laneboysrc/rc-light-controller/mk4-tlc5940-lpc812/tools/webserial-programmer/webapp/README.md

This is a stand-alone webapp that implements the user interface and business logic for programming a .HEX file into the NXP LPC812, LPC832 and LPC824 MCU using an off-the-shelf USB-to-Serial adapter.

Note that a driver for the USB-to-Serial adapter must be installed.

## Build (bundling all source files into a single HTML document)

    ./inline-media.py index.html >../../../../gh-pages/webserial-programmer.html
