laneboysrc/rc-light-controller/doc/Light controller typical package contents.jpg

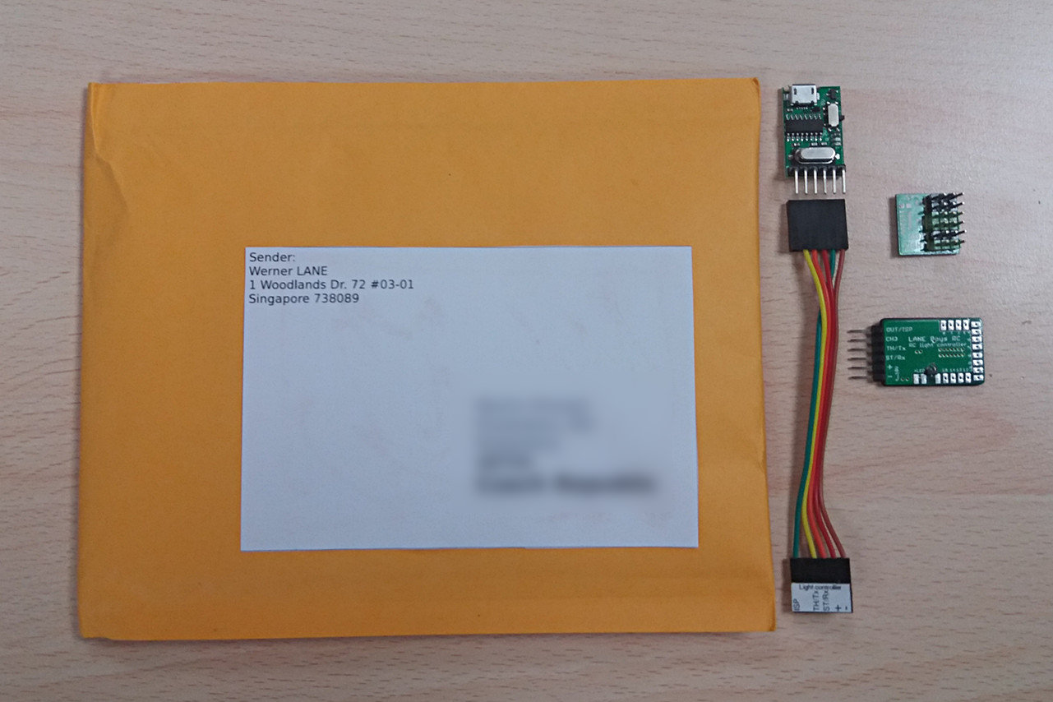
doc/Light controller typical package contents.jpg
