laneboysrc/rc-light-controller/doc/light-controller-mk4-tlc5940-lpc812-rev2.jpg

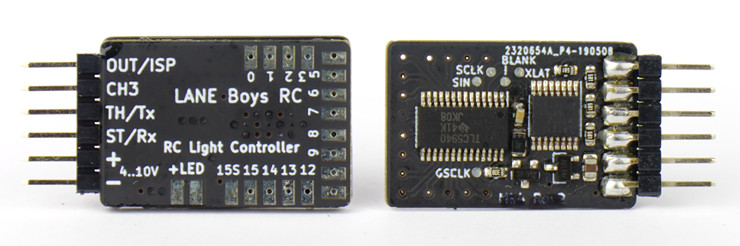
doc/light-controller-mk4-tlc5940-lpc812-rev2.jpg
