laneboysrc/rc-light-controller/doc/mk4-closeup.jpg

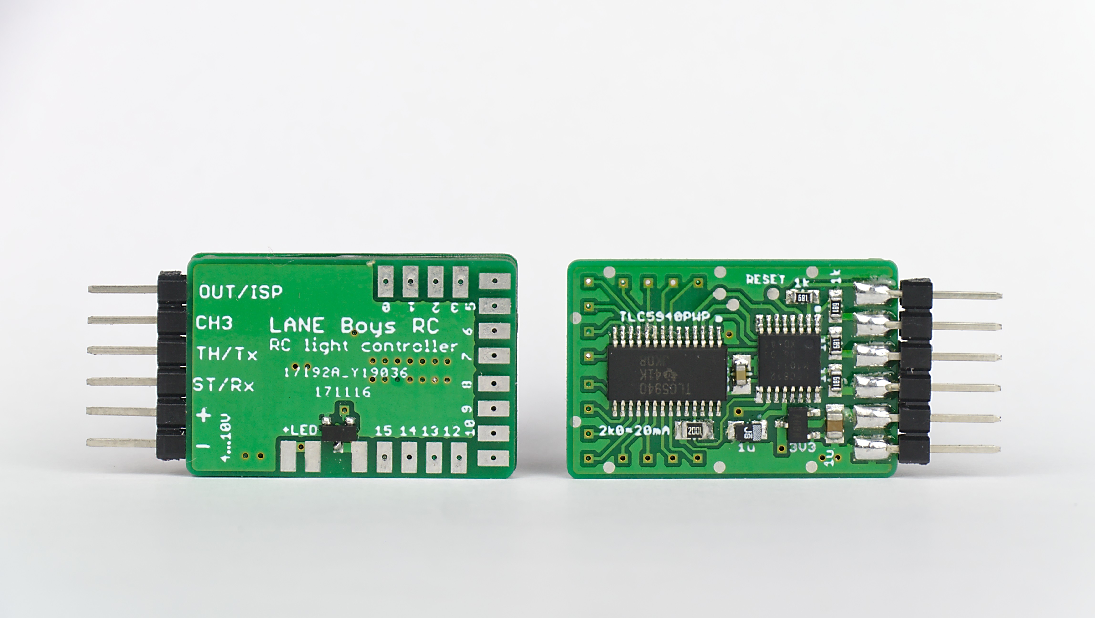
doc/mk4-closeup.jpg
