laneboysrc/rc-light-controller/doc/mk4-rev7-closeup.jpg

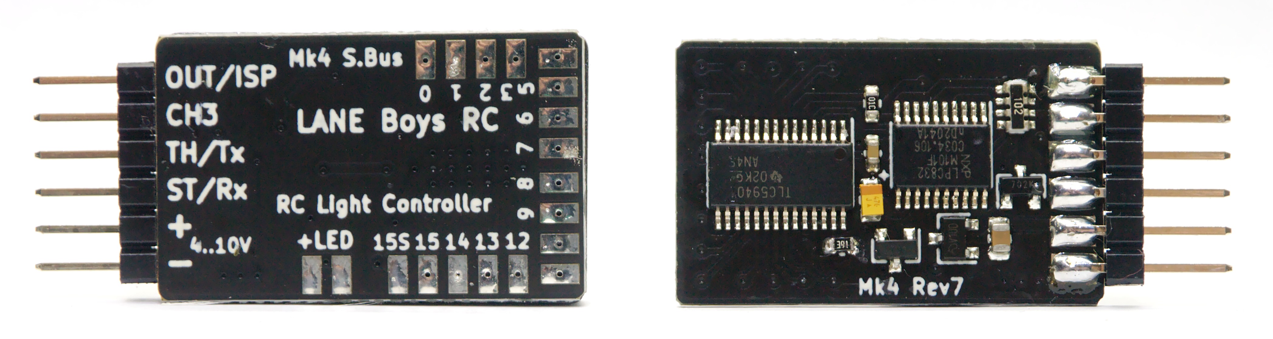
doc/mk4-rev7-closeup.jpg
