laneboysrc/rc-light-controller/doc/mk4-rev7-sbus.jpg

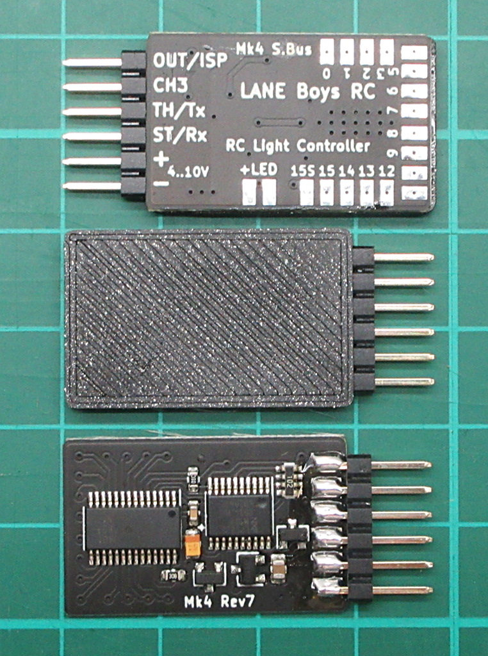
doc/mk4-rev7-sbus.jpg
