laneboysrc/rc-light-controller/doc/mk4-rev7.jpg

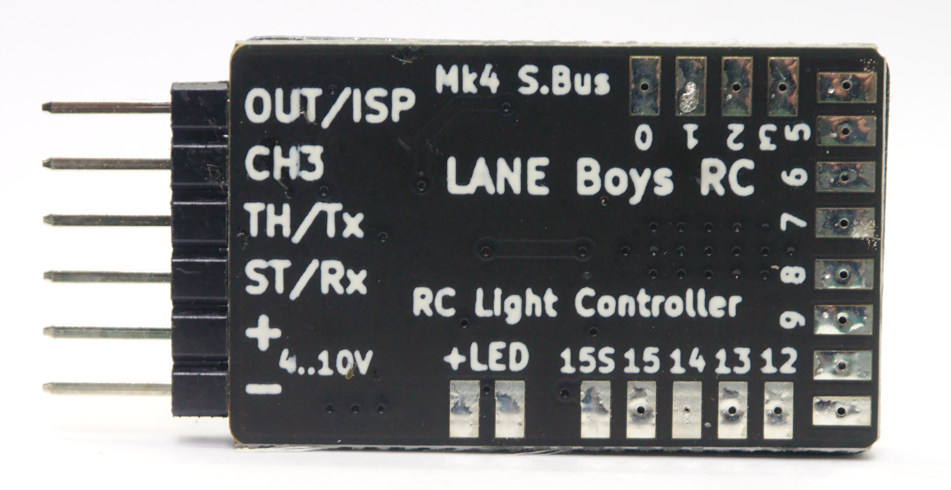
doc/mk4-rev7.jpg
