laneboysrc/rc-light-controller/doc/mk4-single-closeup.jpg

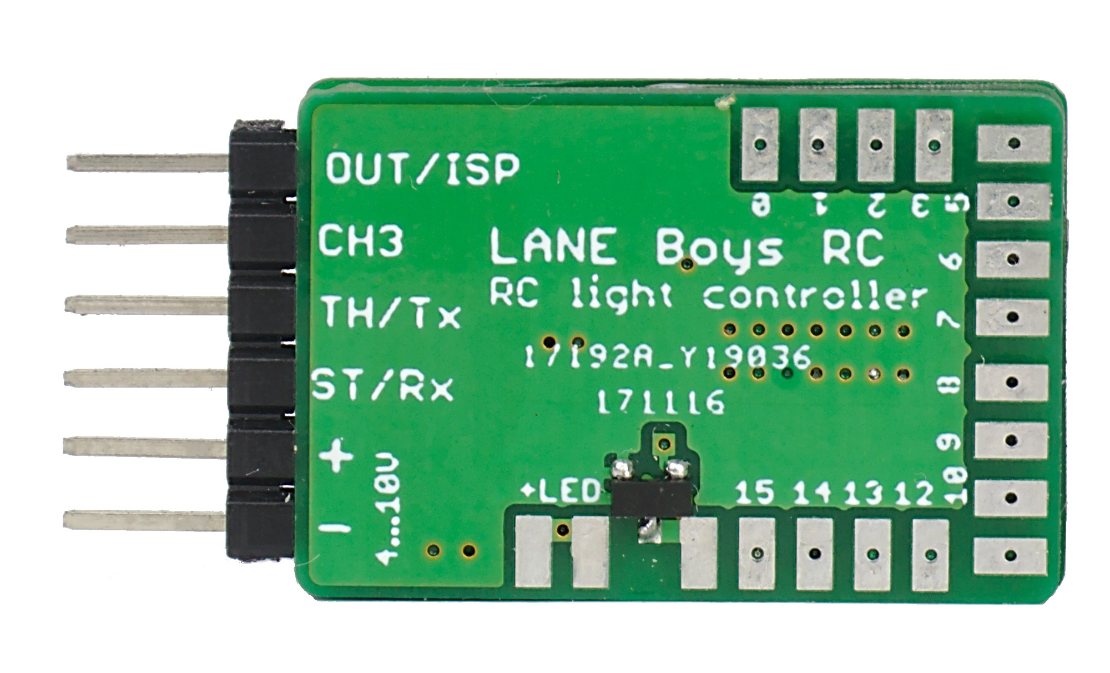
doc/mk4-single-closeup.jpg
