laneboysrc/rc-light-controller/doc/mk4p-connector-side.jpg

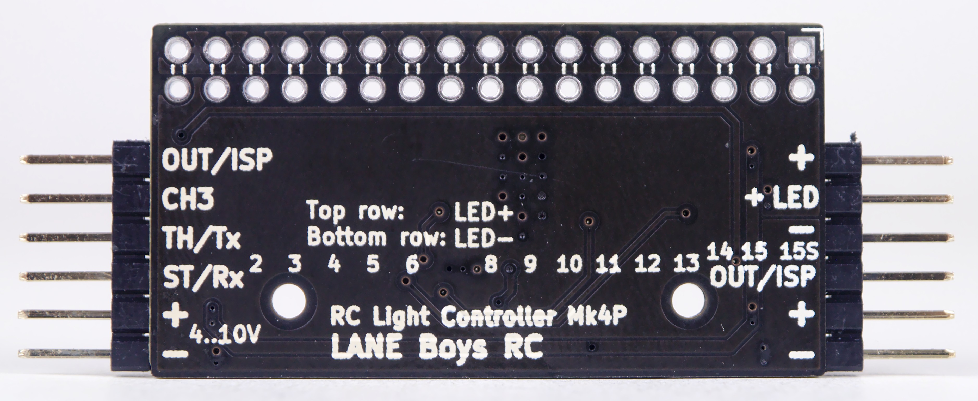
doc/mk4p-connector-side.jpg
