laneboysrc/rc-light-controller/doc/mk4p-front-and-back.jpg

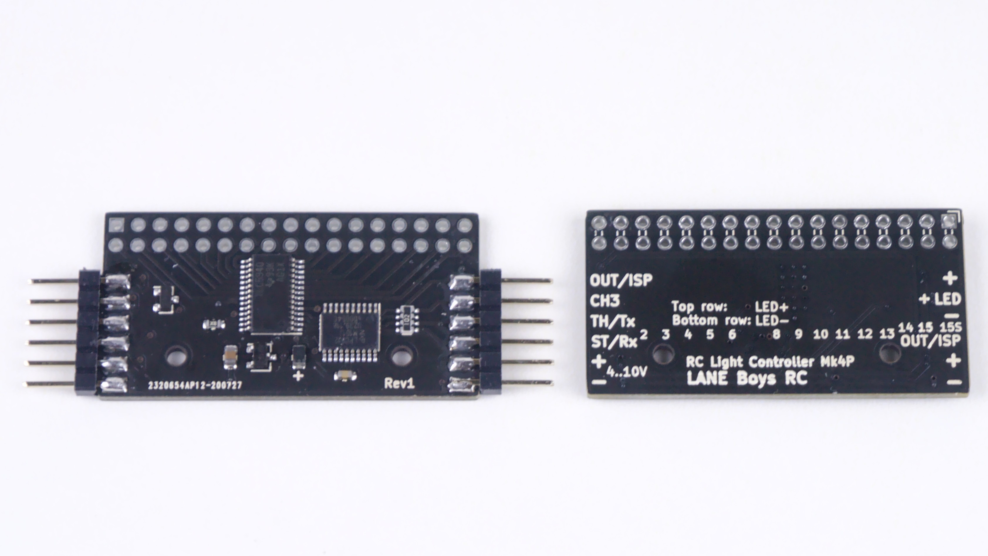
doc/mk4p-front-and-back.jpg
