laneboysrc/rc-light-controller/doc/mk4p-mk4s-led-connector.jpg

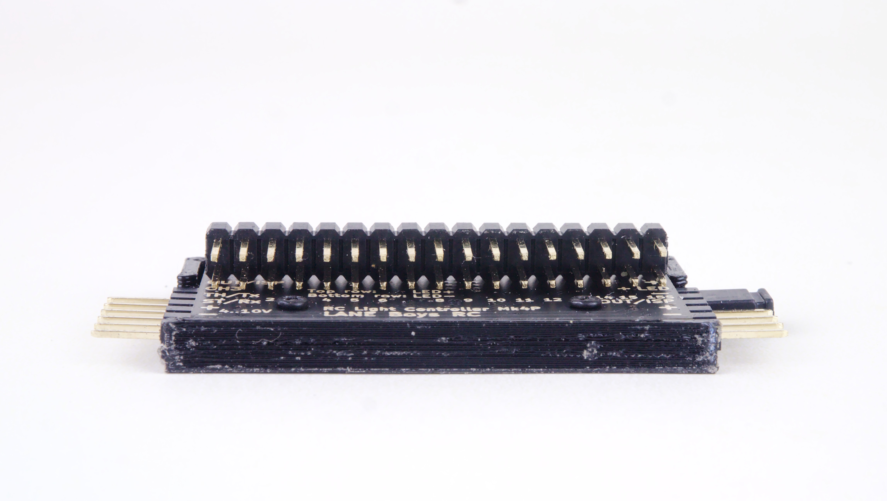
doc/mk4p-mk4s-led-connector.jpg
