laneboysrc/rc-light-controller/doc/mk4p-mk4s-led-supply-options.jpg

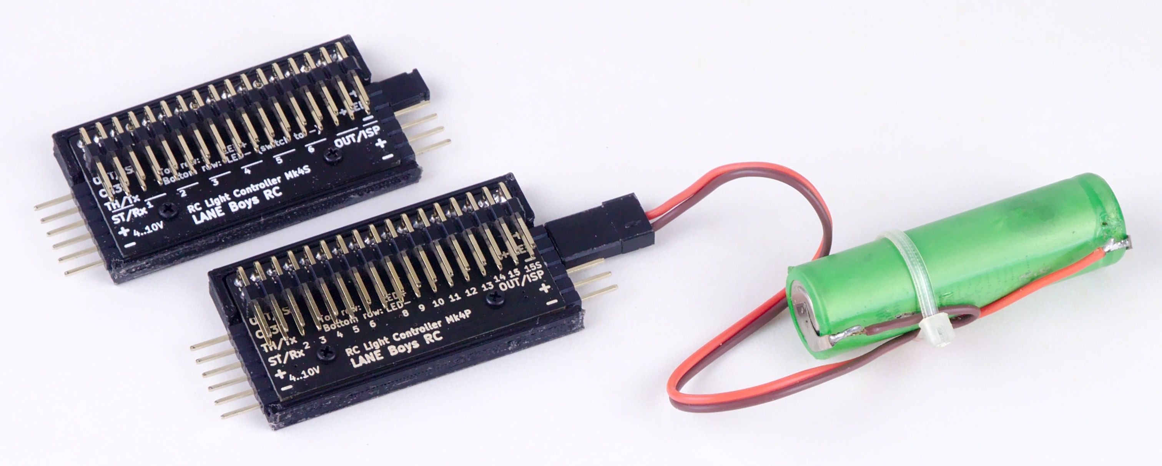
doc/mk4p-mk4s-led-supply-options.jpg
