laneboysrc/rc-light-controller/doc/mk4p-mk4s-together.jpg

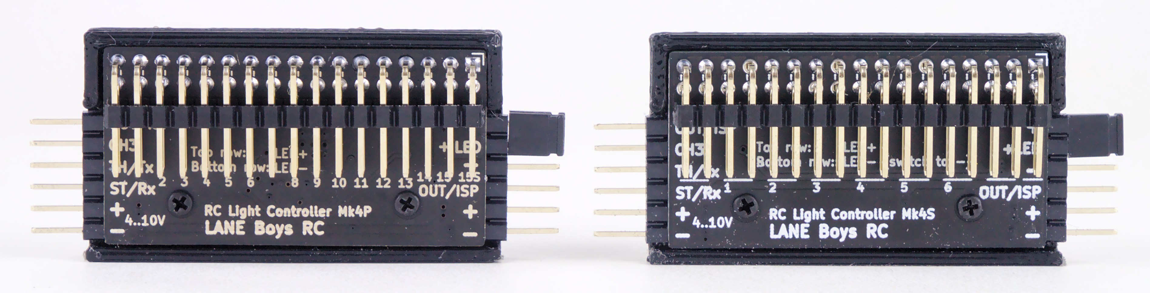
doc/mk4p-mk4s-together.jpg
