laneboysrc/rc-light-controller/doc/mk4s-connector-side.jpg

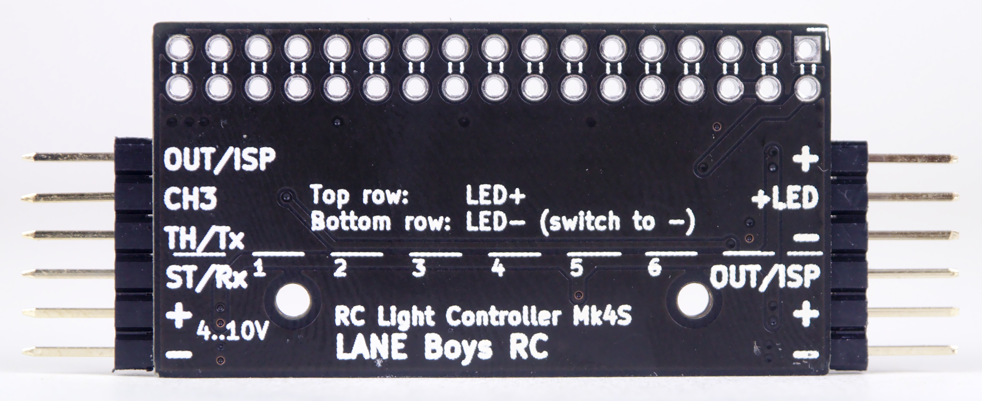
doc/mk4s-connector-side.jpg
