laneboysrc/rc-light-controller/doc/mk4s-front-and-back.jpg

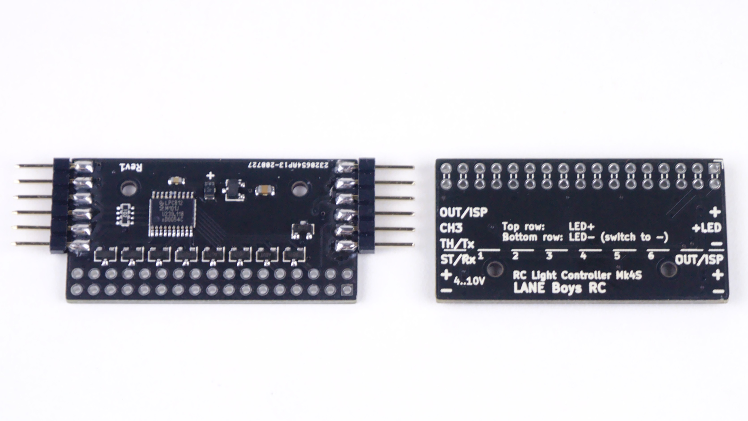
doc/mk4s-front-and-back.jpg
