laneboysrc/rc-light-controller/doc/servo-connected-to-light-controller.png

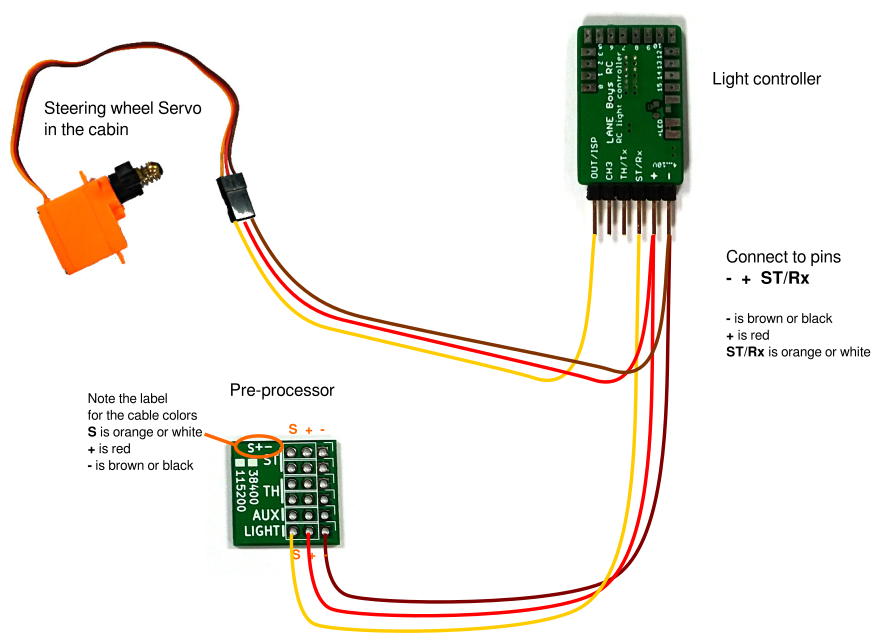
doc/servo-connected-to-light-controller.png
