laneboysrc/rc-light-controller/doc/servo-reader-custom-cable.jpg

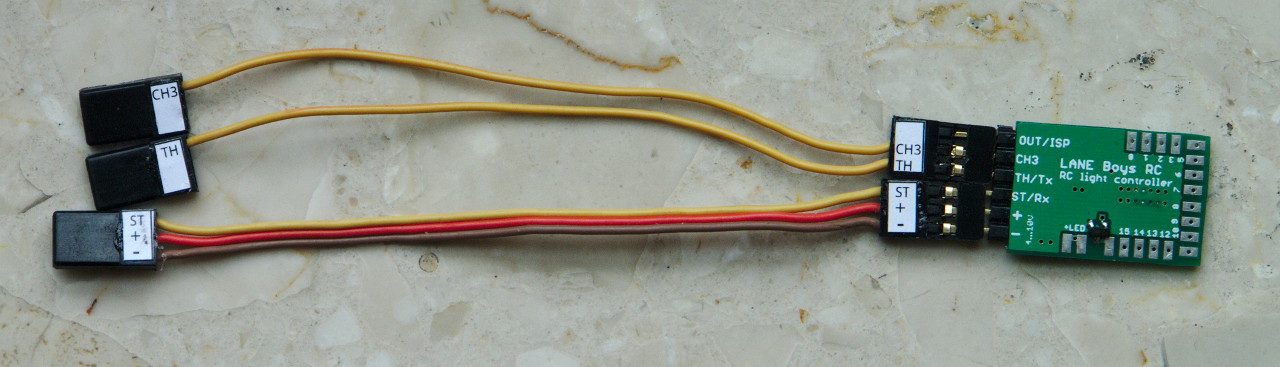
doc/servo-reader-custom-cable.jpg
