laneboysrc/rc-light-controller/doc/src/esc.jpg

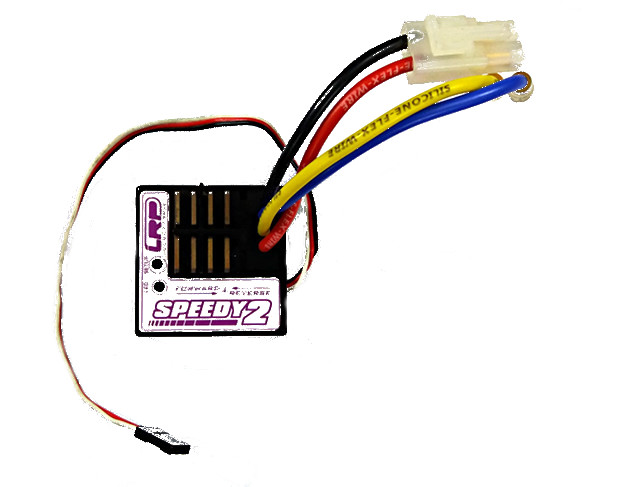
doc/src/esc.jpg
