laneboysrc/rc-light-controller/doc/src/lcp81x_isp..png

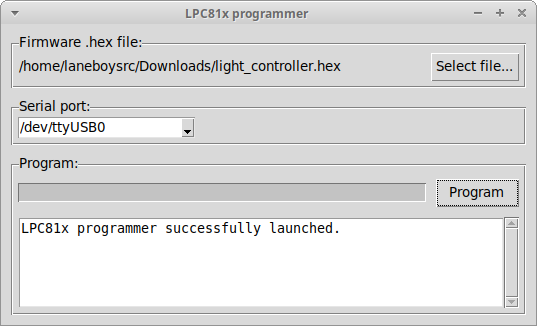
doc/src/lcp81x_isp..png
