laneboysrc/rc-light-controller/doc/src/led_smd_sizes.jpg

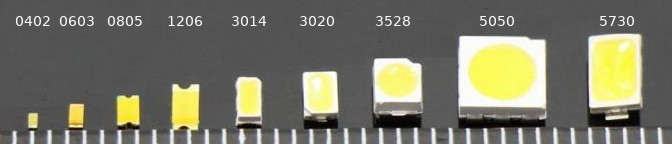
doc/src/led_smd_sizes.jpg
