laneboysrc/rc-light-controller/doc/src/led_throughole.jpg

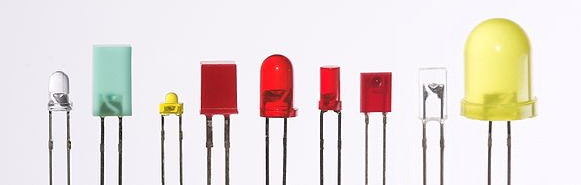
doc/src/led_throughole.jpg
