laneboysrc/rc-light-controller/doc/src/mk4p-rev3-highlighted.jpg

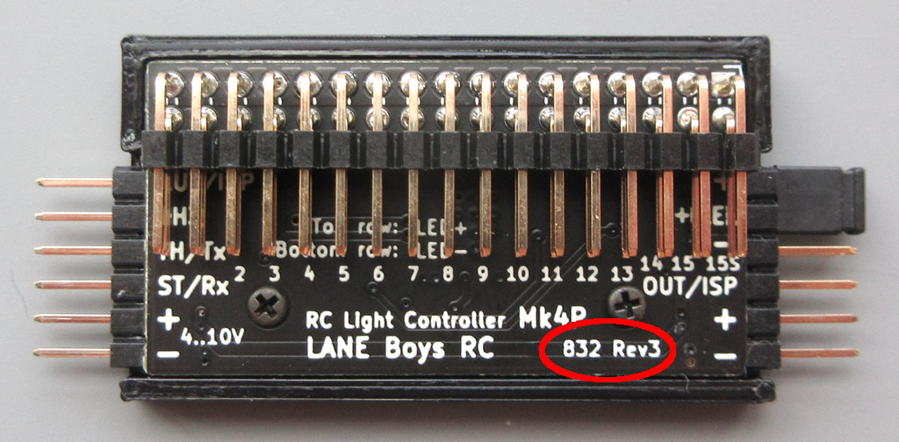
doc/src/mk4p-rev3-highlighted.jpg
