laneboysrc/rc-light-controller/doc/src/preprocessor-5ch.png

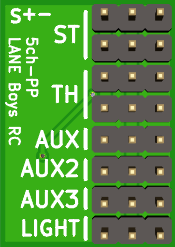
doc/src/preprocessor-5ch.png
