laneboysrc/rc-light-controller/doc/src/pushbutton-round.png

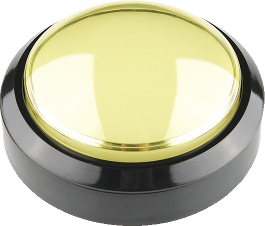
doc/src/pushbutton-round.png
