laneboysrc/rc-light-controller/doc/src/pushbutton.jpg

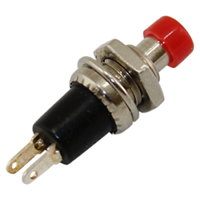
doc/src/pushbutton.jpg
