laneboysrc/rc-light-controller/doc/src/receiver-FGr4S.png

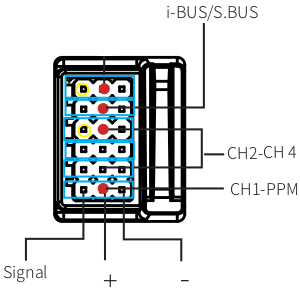
doc/src/receiver-FGr4S.png
