laneboysrc/rc-light-controller/doc/src/servo-pos1.png

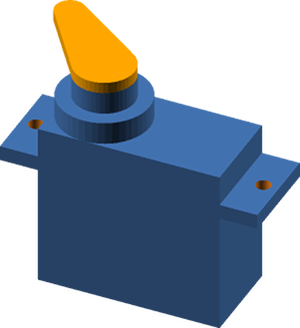
doc/src/servo-pos1.png
