laneboysrc/rc-light-controller/doc/src/servo-pos2.png

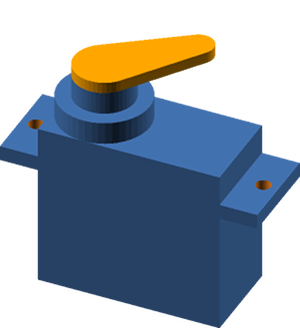
doc/src/servo-pos2.png
