laneboysrc/rc-light-controller/doc/src/servo-reader-diagram-master-slave.png

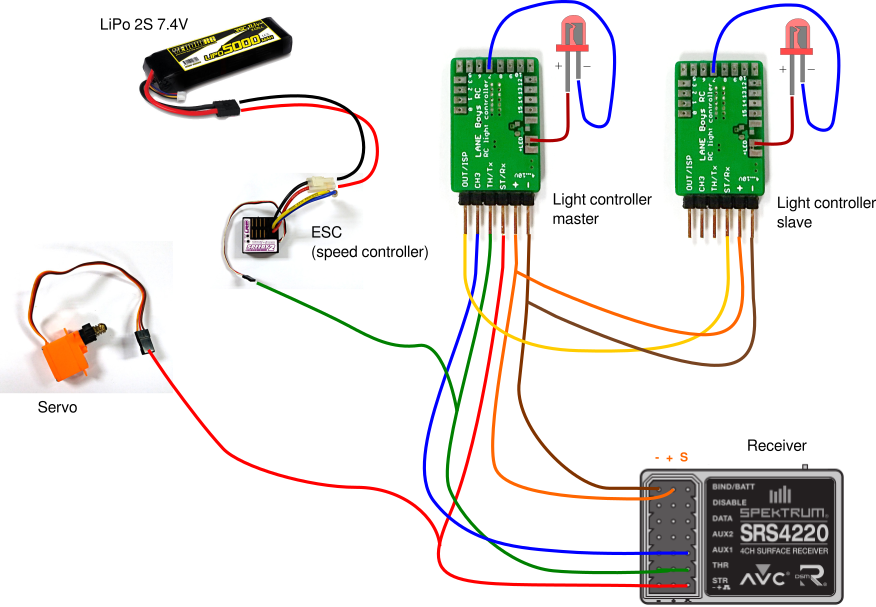
doc/src/servo-reader-diagram-master-slave.png
