laneboysrc/rc-light-controller/doc/src/servo.jpg

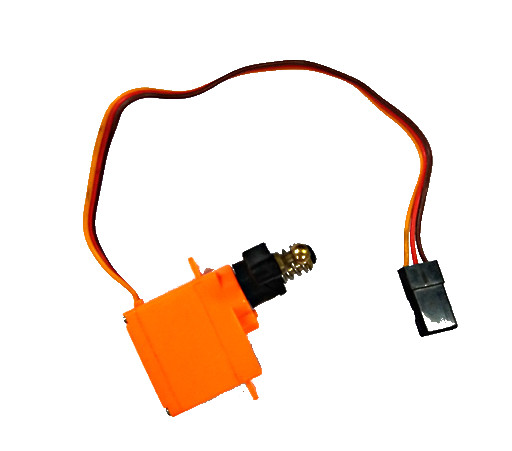
doc/src/servo.jpg
