laneboysrc/rc-light-controller/doc/src/slide-switch.png

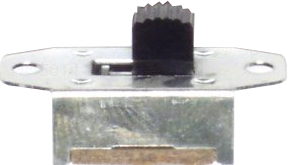
doc/src/slide-switch.png
