laneboysrc/rc-light-controller/doc/src/up-down-button.png

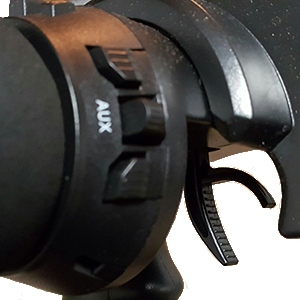
doc/src/up-down-button.png
