laneboysrc/rc-light-controller/doc/src/usb-to-serial-back.jpg

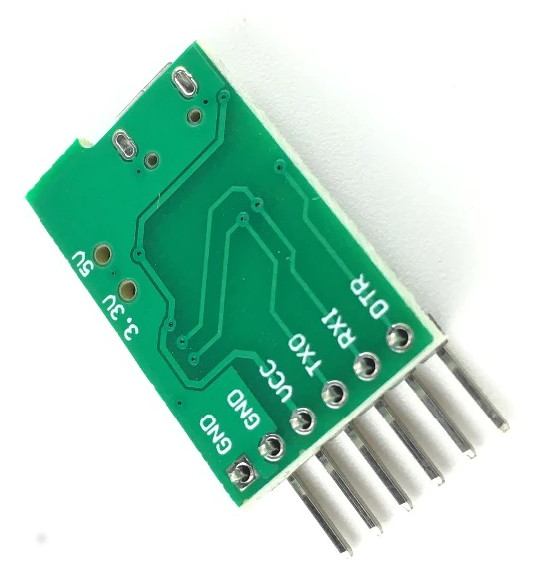
doc/src/usb-to-serial-back.jpg
