laneboysrc/rc-light-controller/doc/src/usb-to-serial-front.jpg

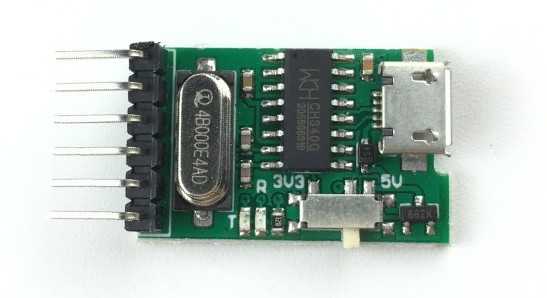
doc/src/usb-to-serial-front.jpg
