laneboysrc/rc-light-controller/doc/src/webusb-programmer-rev3.jpg

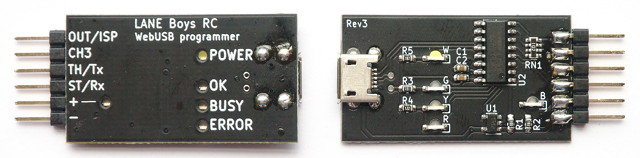
doc/src/webusb-programmer-rev3.jpg
