laneboysrc/rc-light-controller/doc/src/webusb-programming.png

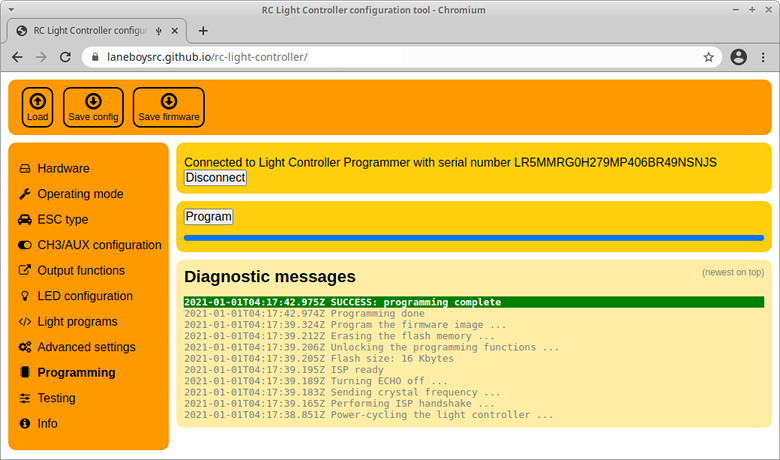
doc/src/webusb-programming.png
