laneboysrc/rc-light-controller/mk4-tlc5940-lpc812/tools/configurator/src/mk4.png

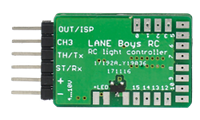
mk4-tlc5940-lpc812/tools/configurator/src/mk4.png
