laneboysrc/rc-light-controller/preprocessor/pre-processor-programming.png

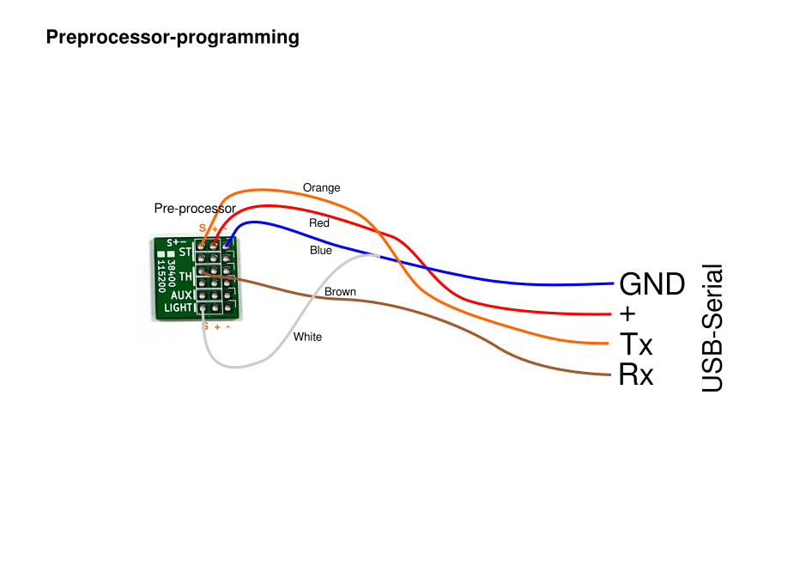
preprocessor/pre-processor-programming.png
