laneboysrc/rc-light-controller/preprocessor/servo-and-esc-wire-splitter/01-distribution-board-top.jpg

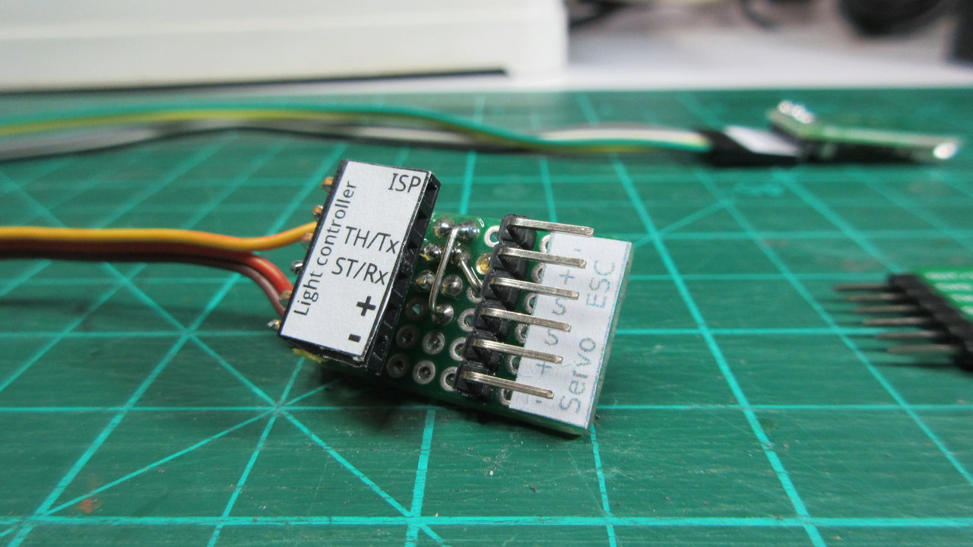
preprocessor/servo-and-esc-wire-splitter/01-distribution-board-top.jpg
