laneboysrc/rc-light-controller/preprocessor/servo-and-esc-wire-splitter/02-distribution-board-bottom.jpg

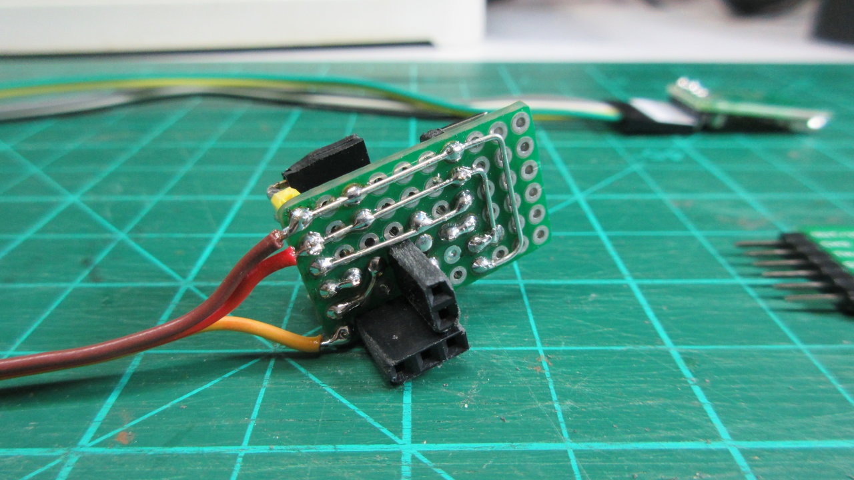
preprocessor/servo-and-esc-wire-splitter/02-distribution-board-bottom.jpg
