laneboysrc/rc-light-controller/preprocessor/servo-and-esc-wire-splitter/03-servo-and-esc-connected.jpg

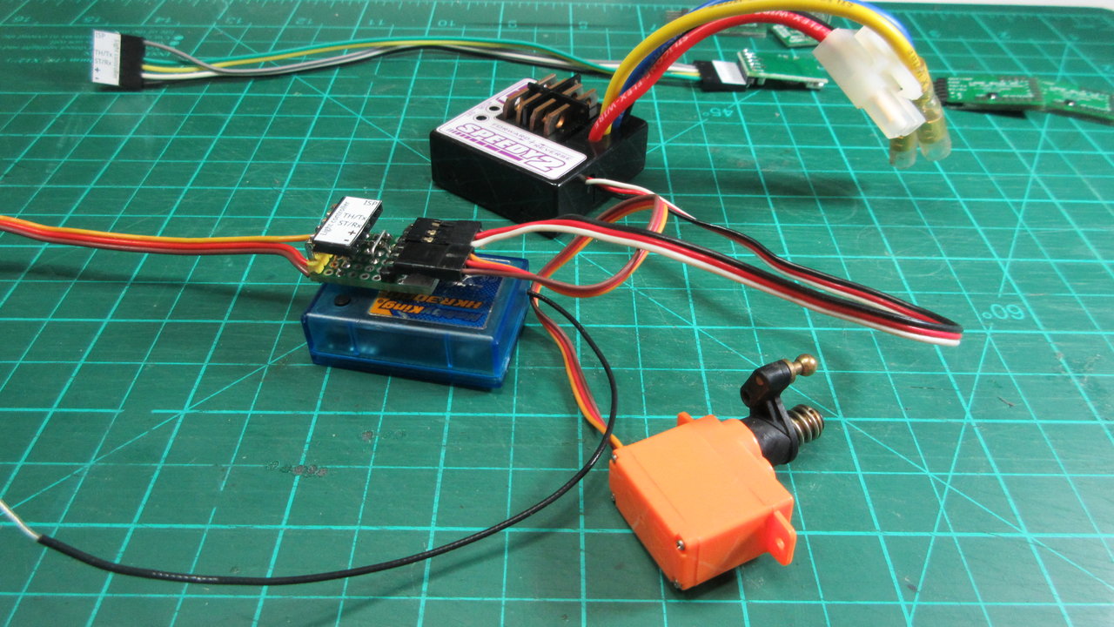
preprocessor/servo-and-esc-wire-splitter/03-servo-and-esc-connected.jpg
