laneboysrc/rc-light-controller/preprocessor/servo-and-esc-wire-splitter/04-servo-and-esc-connected-closeup.jpg

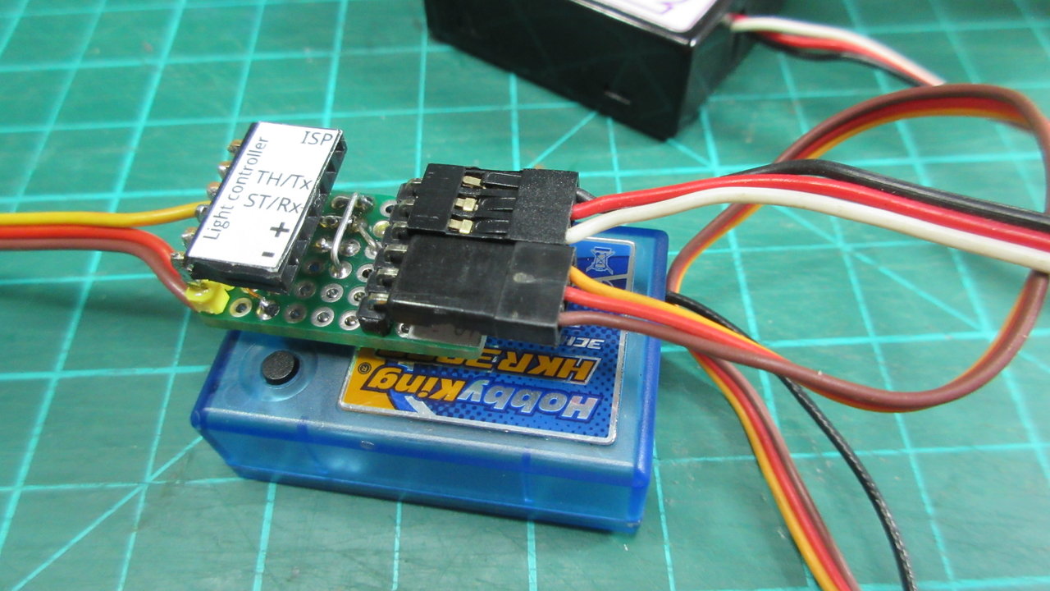
preprocessor/servo-and-esc-wire-splitter/04-servo-and-esc-connected-closeup.jpg
