laneboysrc/rc-light-controller/preprocessor/servo-and-esc-wire-splitter/05-light-controller-connected.jpg

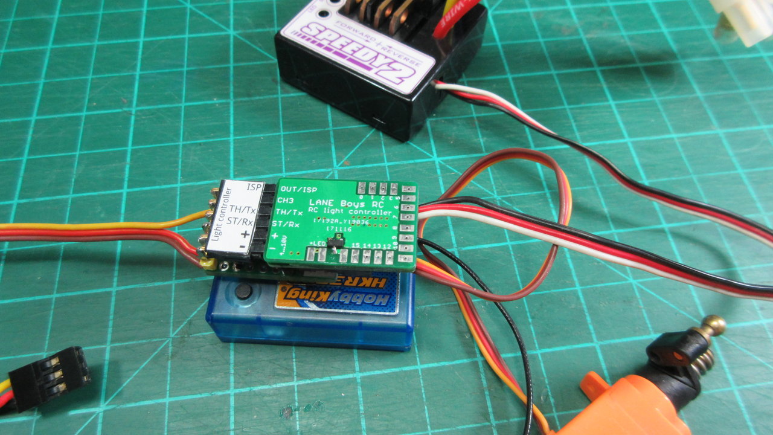
preprocessor/servo-and-esc-wire-splitter/05-light-controller-connected.jpg
