laneboysrc/rc-light-controller/preprocessor/servo-and-esc-wire-splitter/06-all-connections.jpg

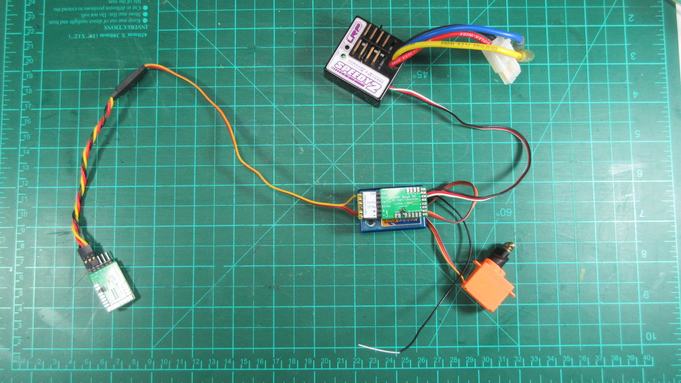
preprocessor/servo-and-esc-wire-splitter/06-all-connections.jpg
