laneboysrc/rc-light-controller/doc/src/webusb-step1.png

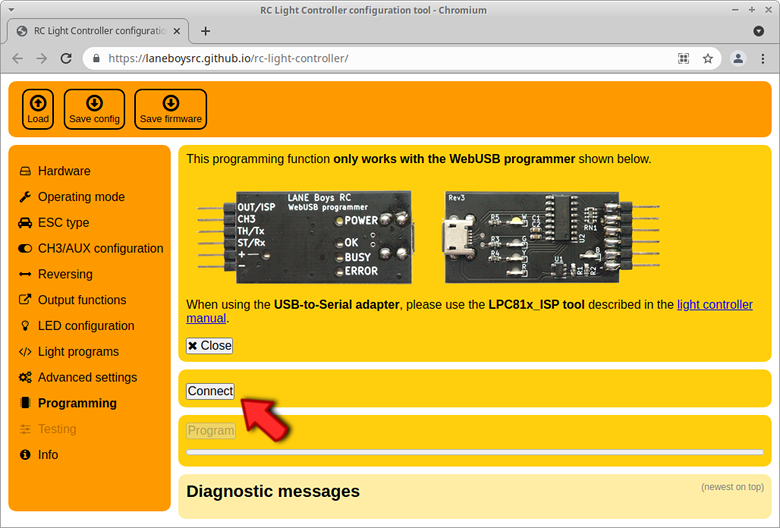
doc/src/webusb-step1.png
