laneboysrc/rc-light-controller/mk4-tlc5940-lpc812/configurations/light_controller.config.land-rover-d110-wiring-diagram.png

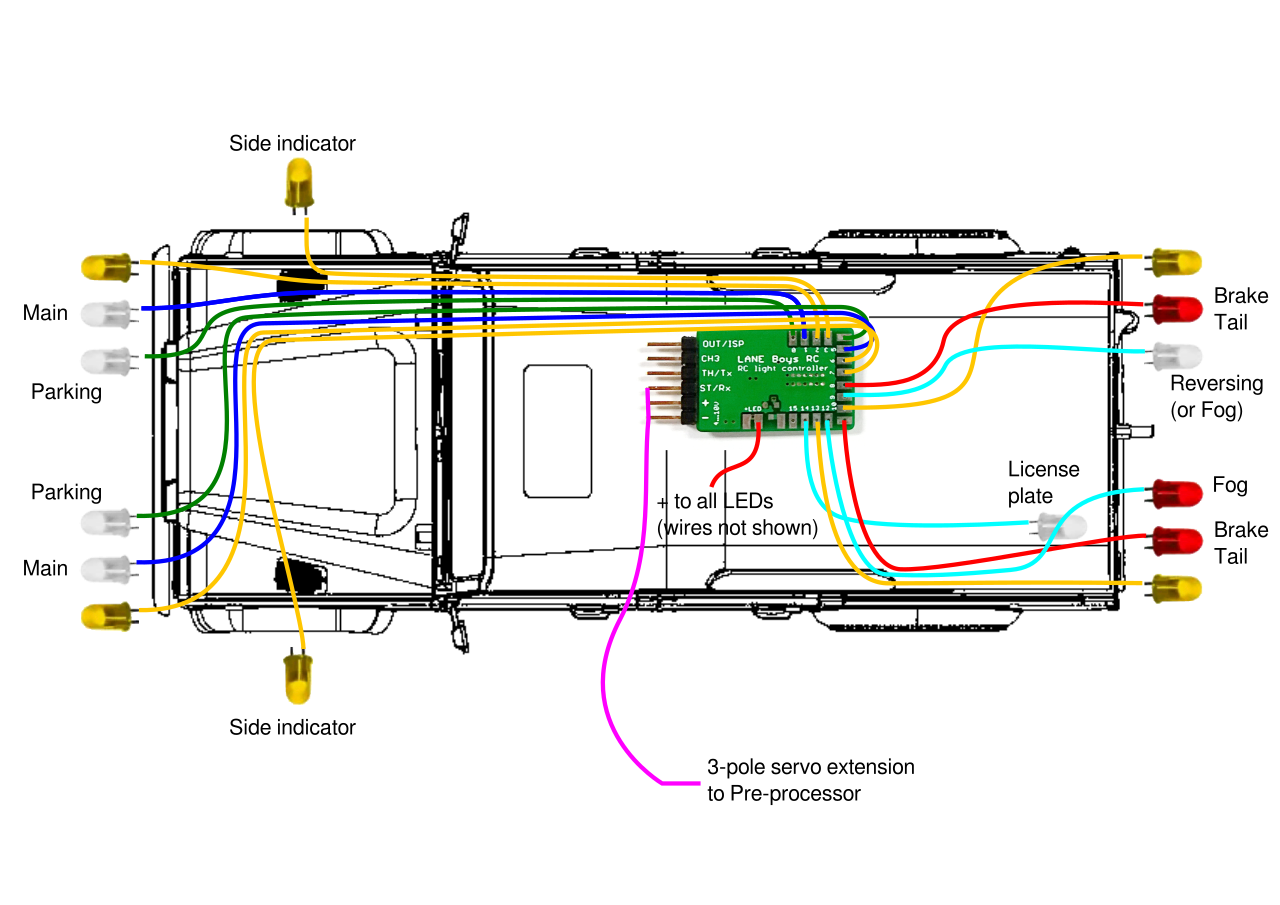
mk4-tlc5940-lpc812/configurations/light_controller.config.land-rover-d110-wiring-diagram.png
