laneboysrc/rc-light-controller/preprocessor/servo-and-esc-wire-splitter/light-controller-distribution-board-wiring.jpg

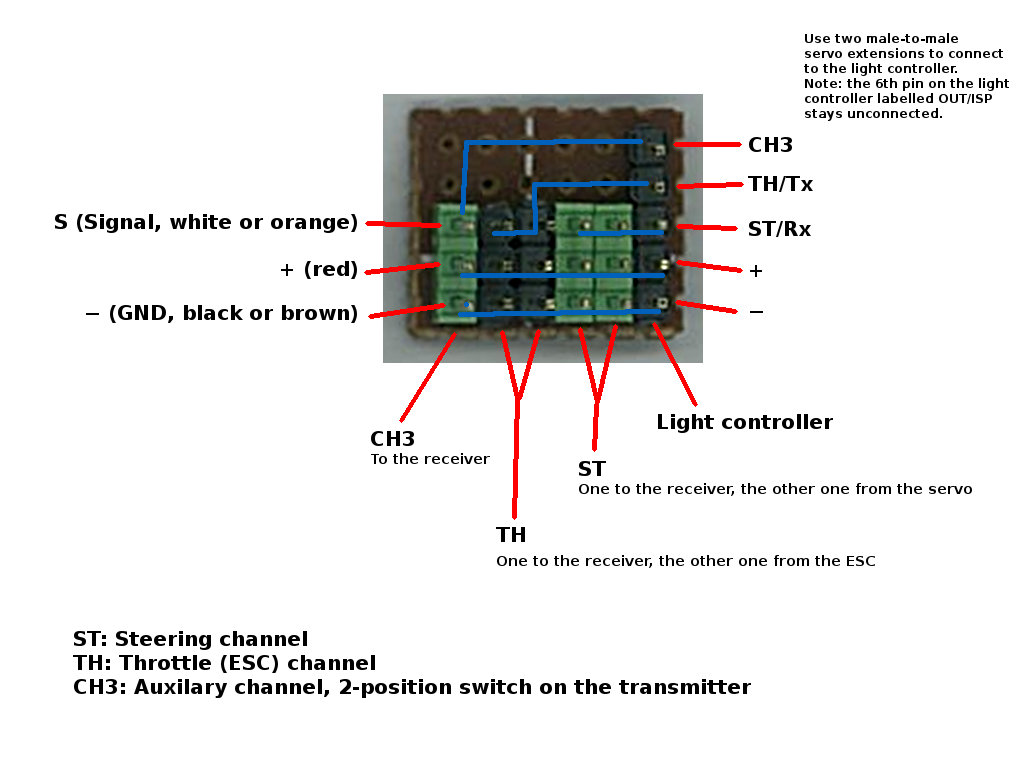
preprocessor/servo-and-esc-wire-splitter/light-controller-distribution-board-wiring.jpg
