laneboysrc/rc-light-controller/doc/src/webusb-testing.png

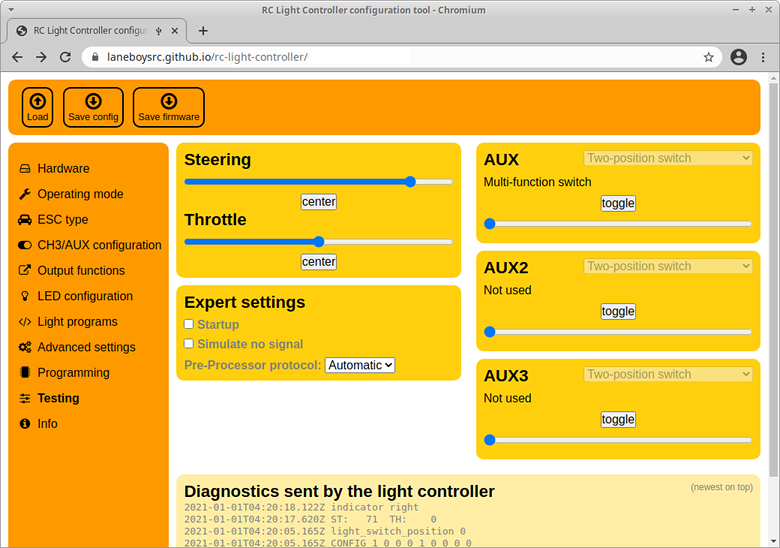
doc/src/webusb-testing.png
