laneboysrc/rc-light-controller/mk4-tlc5940-lpc812/configurations/light_controller.config.school-bus.txt

{
  "config": {
    "firmware_version": 55,
    "mode": 1,
    "esc_mode": 0,
    "slave_output": false,
    "preprocessor_output": false,
    "winch_output": false,
    "steering_wheel_servo_output": true,
    "gearbox_servo_output": false,
    "ws2811_output": false,
    "ch3_is_local_switch": false,
    "ch3_is_momentary": false,
    "auto_brake_lights_forward_enabled": true,
    "auto_brake_lights_reverse_enabled": true,
    "ch3_is_two_button": false,
    "reverse_st": false,
    "reverse_th": false,
    "reverse_aux": false,
    "reverse_aux2": false,
    "reverse_aux3": false,
    "auto_brake_counter_value_forward_min": 25,
    "auto_brake_counter_value_forward_max": 125,
    "auto_brake_counter_value_reverse_min": 25,
    "auto_brake_counter_value_reverse_max": 125,
    "auto_reverse_counter_value_min": 40,
    "auto_reverse_counter_value_max": 100,
    "brake_disarm_counter_value": 50,
    "blink_counter_value": 17,
    "indicator_idle_time_value": 25,
    "indicator_off_timeout_value": 100,
    "centre_threshold_low": 8,
    "centre_threshold_high": 12,
    "blink_threshold": 30,
    "light_switch_positions": 1,
    "initial_light_switch_position": 0,
    "initial_endpoint_delta": 250,
    "ch3_multi_click_timeout": 25,
    "baudrate": 115200,
    "no_signal_timeout": 25,
    "number_of_gears": 2,
    "gearbox_servo_active_time": 50,
    "gearbox_servo_idle_time": 450,
    "servo_pulse_min": 600,
    "servo_pulse_max": 2500,
    "startup_time": 100,
    "multi_aux": true,
    "shelf_queen_mode": true,
    "us_style_combined_lights": true,
    "gearbox_light_program_control": false,
    "light_program_servo_output": false,
    "indicators_while_driving": false,
    "require_extra_click": false,
    "prefer_all_lights_off": false,
    "invert_out15s": false,
    "assign_uart_to_out": false,
    "blink_counter_value_dark": 17,
    "aux_type": 0,
    "aux_function": 1,
    "aux2_type": 3,
    "aux2_function": 0,
    "aux3_type": 0,
    "aux3_function": 0,
    "aux_centre_threshold_low": -10,
    "aux_centre_threshold_high": 10,
    "aux_left_centre_threshold_low": -40,
    "aux_left_centre_threshold_high": -30,
    "aux_centre_right_threshold_low": 30,
    "aux_centre_right_threshold_high": 40,
    "diagnostics_brightness": 255,
    "channel_offset": 3,
    "light_switch_hysteresis": 50,
    "light_switch_centers": [
      0,
      0,
      0,
      0,
      0,
      0,
      0,
      0,
      0
    ]
  },
  "local_leds": {
    "0": {
      "max_change_per_systick": 0,
      "reduction_percent": 0,
      "weak_light_switch_position0": false,
      "weak_light_switch_position1": false,
      "weak_light_switch_position2": false,
      "weak_light_switch_position3": false,
      "weak_light_switch_position4": false,
      "weak_light_switch_position5": false,
      "weak_light_switch_position6": false,
      "weak_light_switch_position7": false,
      "weak_light_switch_position8": false,
      "weak_tail_light": false,
      "weak_brake_light": false,
      "weak_reversing_light": false,
      "weak_indicator_left": false,
      "weak_indicator_right": false,
      "always_on": 0,
      "light_switch_position0": 0,
      "light_switch_position1": 0,
      "light_switch_position2": 0,
      "light_switch_position3": 0,
      "light_switch_position4": 0,
      "light_switch_position5": 0,
      "light_switch_position6": 0,
      "light_switch_position7": 0,
      "light_switch_position8": 0,
      "tail_light": 0,
      "brake_light": 0,
      "reversing_light": 0,
      "indicator_left": 0,
      "indicator_right": 0,
      "diagnostics": 0,
      "name": ""
    },
    "1": {
      "max_change_per_systick": 0,
      "reduction_percent": 0,
      "weak_light_switch_position0": false,
      "weak_light_switch_position1": false,
      "weak_light_switch_position2": false,
      "weak_light_switch_position3": false,
      "weak_light_switch_position4": false,
      "weak_light_switch_position5": false,
      "weak_light_switch_position6": false,
      "weak_light_switch_position7": false,
      "weak_light_switch_position8": false,
      "weak_tail_light": false,
      "weak_brake_light": false,
      "weak_reversing_light": false,
      "weak_indicator_left": false,
      "weak_indicator_right": false,
      "always_on": 0,
      "light_switch_position0": 0,
      "light_switch_position1": 0,
      "light_switch_position2": 0,
      "light_switch_position3": 0,
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
      "indicator_right": 0,
      "diagnostics": 0,
      "name": ""
    },
    "15": {
      "max_change_per_systick": 0,
      "reduction_percent": 0,
      "weak_light_switch_position0": false,
      "weak_light_switch_position1": false,
      "weak_light_switch_position2": false,
      "weak_light_switch_position3": false,
      "weak_light_switch_position4": false,
      "weak_light_switch_position5": false,
      "weak_light_switch_position6": false,
      "weak_light_switch_position7": false,
      "weak_light_switch_position8": false,
      "weak_tail_light": false,
      "weak_brake_light": false,
      "weak_reversing_light": false,
      "weak_indicator_left": false,
      "weak_indicator_right": false,
      "always_on": 0,
      "light_switch_position0": 0,
      "light_switch_position1": 0,
      "light_switch_position2": 0,
      "light_switch_position3": 0,
      "light_switch_position4": 0,
      "light_switch_position5": 0,
      "light_switch_position6": 0,
      "light_switch_position7": 0,
      "light_switch_position8": 0,
      "tail_light": 0,
      "brake_light": 0,
      "reversing_light": 0,
      "indicator_left": 0,
      "indicator_right": 0,
      "diagnostics": 0,
      "name": ""
    },
    "led_count": 16
  },
  "gamma": {
    "gamma_value": "1.8"
  },
  "light_programs": "// Canada school bus yellow and red warning light\n// Based on https://www.youtube.com/watch?v=-NQjBX6ZlSU\n// The school bus has 8 lights: \n// OUT0: yellow front left\n// OUT1: red left front \n// OUT2: red right front \n// OUT3: yellow right front \n// OUT4: yellow left rear\n// OUT5: red left rear\n// OUT6: red right rear\n// OUT7: yellow right rear\n//\n// A 3-position switch on the transmitter is connected to AUX2.\n// The switch sequence is off -> yellow -> red\n//\n// The AUX2 channel is monitored in a \"run always\" light program\n// and setting the special variables program-state-0 and program-state1.\n// A light program for the YELLOW LEDs is run when program-state-0 is set to \"1\".\n// A light program for the RED LEDs is run when program-state-1 is set to \"1\".\n\nrun always\n\nloop:\n\tsleep 20\n    if aux2 < -33\n    goto off\n    if aux2 < 33\n    goto yellow\n    // if aux2 >= 33 then do red\nred:    \n\t// Switch off yellow, turn on red\n\tprogram-state-0 = 0\n\tprogram-state-1 = 1\t\n    goto loop\n\nyellow:    \n\t// Switch on yellow, turn of red\n\tprogram-state-0 = 1\n\tprogram-state-1 = 0\n    goto loop\n\noff:    \n\t// Switch of yellow and red\n\tprogram-state-0 = 0\n\tprogram-state-1 = 0\n    goto loop\n\nend\n\n// Light program for flashing of yellow lights\nrun when program-state-0\n\nled ylf = led[1] \t// yellow left front\nled yrf = led[2] \t// yellow right front\nled ylr = led[5] \t// yellow left rear\nled yrr = led[6] \t// yellow right rear\n\n// According to the video the lights never go fully dark, \n// so we toggle between a minimum and maximum brightness\nconst BRIGHTNESS_MIN = 15\nconst BRIGHTNESS_MAX = 100\n// FADE_TIMING determines how quickly the LEDs fade. \n// Expimentation is required to determine which value \n// gives a good experience.\nconst FADE_TIMING = 3\n// According to the video the blink sequence is \n// 0.5 seconds off, 0.5 seconds on.\nconst TIME_PERIOD = 500\n\nloop:\n\tfade all leds stepsize FADE_TIMING\n    ylf, ylr = BRIGHTNESS_MAX\n    yrf, yrr = BRIGHTNESS_MIN\n    sleep TIME_PERIOD\n    ylf, ylr = BRIGHTNESS_MIN\n    yrf, yrr = BRIGHTNESS_MAX\n    sleep TIME_PERIOD\n\tgoto loop\n\nend\n\n// Light program for flashing of red lights\nrun when program-state-1\n\nled rlf = led[0] \t// red left front\nled rrf = led[3] \t// red right front\nled rlr = led[4] \t// red left rear\nled rrr = led[7] \t// red right rear\n\nconst BRIGHTNESS_MIN = 15\nconst BRIGHTNESS_MAX = 100\nconst FADE_TIMING = 3\nconst TIME_PERIOD = 500\n\nloop:\n\tfade all leds stepsize FADE_TIMING\n    rlf, rlr = BRIGHTNESS_MAX\n    rrf, rrr = BRIGHTNESS_MIN\n    sleep TIME_PERIOD\n    rlf, rlr = BRIGHTNESS_MIN    \n    rrf, rrr = BRIGHTNESS_MAX\n    sleep TIME_PERIOD\n\tgoto loop\n\nend"
}
