laneboysrc/rc-light-controller/mk4-tlc5940-lpc812/configurations/light_controller.config.up-down-sequential-light-switch.txt

{
  "config": {
    "firmware_version": 44,
    "mode": 1,
    "esc_mode": 0,
    "slave_output": false,
    "preprocessor_output": false,
    "steering_wheel_servo_output": true,
    "gearbox_servo_output": false,
    "ch3_is_local_switch": false,
    "ch3_is_momentary": false,
    "auto_brake_lights_forward_enabled": true,
    "auto_brake_lights_reverse_enabled": true,
    "ch3_is_two_button": false,
    "reverse_st": false,
    "reverse_th": false,
    "reverse_aux": false,
    "reverse_aux2": false,
    "reverse_aux3": false,
    "auto_brake_counter_value_forward_min": 25,
    "auto_brake_counter_value_forward_max": 125,
    "auto_brake_counter_value_reverse_min": 25,
    "auto_brake_counter_value_reverse_max": 125,
    "auto_reverse_counter_value_min": 40,
    "auto_reverse_counter_value_max": 100,
    "brake_disarm_counter_value": 50,
    "blink_counter_value": 17,
    "indicator_idle_time_value": 25,
    "indicator_off_timeout_value": 100,
    "centre_threshold_low": 8,
    "centre_threshold_high": 12,
    "blink_threshold": 30,
    "light_switch_positions": 5,
    "initial_light_switch_position": 0,
    "initial_endpoint_delta": 250,
    "ch3_multi_click_timeout": 25,
    "baudrate": 115200,
    "no_signal_timeout": 25,
    "number_of_gears": 2,
    "gearbox_servo_active_time": 50,
    "gearbox_servo_idle_time": 450,
    "servo_pulse_min": 600,
    "servo_pulse_max": 2500,
    "startup_time": 100,
    "multi_aux": true,
    "shelf_queen_mode": true,
    "us_style_combined_lights": true,
    "gearbox_light_program_control": false,
    "light_program_servo_output": false,
    "indicators_while_driving": false,
    "require_extra_click": false,
    "prefer_all_lights_off": false,
    "invert_out15s": false,
    "assign_uart_to_out": false,
    "blink_counter_value_dark": 17,
    "aux_type": 0,
    "aux_function": 1,
    "aux2_type": 3,
    "aux2_function": 0,
    "aux3_type": 0,
    "aux3_function": 0,
    "aux_centre_threshold_low": -10,
    "aux_centre_threshold_high": 10,
    "aux_left_centre_threshold_low": -40,
    "aux_left_centre_threshold_high": -30,
    "aux_centre_right_threshold_low": 30,
    "aux_centre_right_threshold_high": 40,
    "diagnostics_brightness": 255,
    "light_switch_hysteresis": 10,
    "light_switch_centers": [
      -80,
      -40,
      0,
      40,
      80,
      0,
      0,
      0,
      0
    ]
  },
  "local_leds": {
    "0": {
      "max_change_per_systick": 0,
      "reduction_percent": 0,
      "weak_light_switch_position0": false,
      "weak_light_switch_position1": false,
      "weak_light_switch_position2": false,
      "weak_light_switch_position3": false,
      "weak_light_switch_position4": false,
      "weak_light_switch_position5": false,
      "weak_light_switch_position6": false,
      "weak_light_switch_position7": false,
      "weak_light_switch_position8": false,
      "weak_tail_light": false,
      "weak_brake_light": false,
      "weak_reversing_light": false,
      "weak_indicator_left": false,
      "weak_indicator_right": false,
      "always_on": 0,
      "light_switch_position0": 0,
      "light_switch_position1": 255,
      "light_switch_position2": 255,
      "light_switch_position3": 255,
      "light_switch_position4": 255,
      "light_switch_position5": 0,
      "light_switch_position6": 0,
      "light_switch_position7": 0,
      "light_switch_position8": 0,
      "tail_light": 0,
      "brake_light": 0,
      "reversing_light": 0,
      "indicator_left": 0,
      "indicator_right": 0,
      "diagnostics": 0
    },
    "1": {
      "max_change_per_systick": 0,
      "reduction_percent": 0,
      "weak_light_switch_position0": false,
      "weak_light_switch_position1": false,
      "weak_light_switch_position2": false,
      "weak_light_switch_position3": false,
      "weak_light_switch_position4": false,
      "weak_light_switch_position5": false,
      "weak_light_switch_position6": false,
      "weak_light_switch_position7": false,
      "weak_light_switch_position8": false,
      "weak_tail_light": false,
      "weak_brake_light": false,
      "weak_reversing_light": false,
      "weak_indicator_left": false,
      "weak_indicator_right": false,
      "always_on": 0,
      "light_switch_position0": 0,
      "light_switch_position1": 255,
      "light_switch_position2": 255,
      "light_switch_position3": 255,
      "light_switch_position4": 255,
      "light_switch_position5": 0,
      "light_switch_position6": 0,
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
      "weak_tail_light": false,
      "weak_brake_light": false,
      "weak_reversing_light": false,
      "weak_indicator_left": false,
      "weak_indicator_right": false,
      "always_on": 0,
      "light_switch_position0": 0,
      "light_switch_position1": 0,
      "light_switch_position2": 0,
      "light_switch_position3": 0,
      "light_switch_position4": 255,
      "light_switch_position5": 0,
      "light_switch_position6": 0,
      "light_switch_position7": 0,
      "light_switch_position8": 0,
      "tail_light": 0,
      "brake_light": 0,
      "reversing_light": 0,
      "indicator_left": 0,
      "indicator_right": 0,
      "diagnostics": 0
    },
    "led_count": 16
  },
  "gamma": {
    "gamma_value": "1.8"
  },
  "light_programs": "// This light program implements a sequential light switch\n// using an up/down button on a transmitter.\n//\n// This light program requires a 5-channel Pre-Processor.\n// It uses AUX2, but any of the AUX channels can be used.\n//\n// The buttons on the transmitter must have a momentary\n// function: \n// - When no button is pressed, the servo is in the center\n// - While the up button is held, the servo is in position +100\n// - While the down button is held, the servo is in position -100\n\nrun always\n\n// Threshold for the AUX channel to implement a hysteresis\nconst THRESHOLD_LEFT = -66\nconst THRESHOLD_CENTER_LEFT = -33\nconst THRESHOLD_CENTER_RIGHT = 33\nconst THRESHOLD_RIGHT = 66\n\n// Internal state variable to track the AUX signal\nvar state\nconst STATE_WAIT_FOR_CENTER = 0\nconst STATE_CENTER = 1\n\n\nloop:\n\t// We check the AUX channel every 40ms, the\n    // rest of the time the light controller \n    // can do other things\n\tsleep 40\n    \n    // Branch to the action reflecting the current\n    // state\n    if state == STATE_WAIT_FOR_CENTER\n    goto wait_for_center\n    if state == STATE_CENTER\n    goto center\n\n\t// We should never reach here; just in case ...\n    state = STATE_WAIT_FOR_CENTER\n\tgoto loop\n\n\t// Wait for the button to be released (= center).\n    // For the AUX to be in center, the servo signal\n    // must be between THRESHOLD_CENTER_LEFT and\n    // THRESHOLD_CENTER_RIGHT (-33 .. +33)\nwait_for_center:\n\t// If AUX is less than LEFT, the switch is\n    // not in the center\n\tif aux2 < THRESHOLD_CENTER_LEFT\n    goto loop\n\t// If AUX is more than RIGHT, the switch is\n    // not in the center\n\tif aux2 > THRESHOLD_CENTER_RIGHT\n    goto loop\n    // Between LEFT and RIGHT: switch is in the center!\n    state = STATE_CENTER\n\tgoto loop\n    \n    // Switch was centered: detect whether the up\n    // or down button has been pressed\ncenter:\n\t// LEFT threshold exceeded: we have a down button press!\n\tif aux2 < THRESHOLD_LEFT\n    goto down\n\t// RIGHT threshold exceeded: we have an up button press!\n\tif aux2 > THRESHOLD_RIGHT\n    goto up\n\tgoto loop\n\n\t// Down button: decrement the light switch position.\n    // If the light switch position is 0, then we set it\n    // to -1 -- but the light controller checks for that\n    // and \"fixes\" the value back to 0.\ndown:\n\tlight-switch-position -= 1\n    state = STATE_WAIT_FOR_CENTER\n\tgoto loop\n\n\t// Up button: increment the light switch position.\n    // If the light switch ends up beyond the position \n    // defined in the \"LED configuration\" table, the \n    // light controller will \"fix\" it back to the hightest.\n    // used light switch position.\nup:\n\tlight-switch-position += 1\n    state = STATE_WAIT_FOR_CENTER\n\tgoto loop\n\nend"
}
