laneboysrc/rc-light-controller/mk4-tlc5940-lpc812/configurations/light_controller.config.lexus-rcf.txt

{
  "config": {
    "firmware_version": 1,
    "mode": 0,
    "esc_mode": 1,
    "slave_output": false,
    "preprocessor_output": false,
    "winch_output": false,
    "steering_wheel_servo_output": false,
    "gearbox_servo_output": false,
    "ch3_is_local_switch": false,
    "ch3_is_momentary": false,
    "auto_brake_lights_forward_enabled": true,
    "auto_brake_lights_reverse_enabled": true,
    "auto_brake_counter_value_forward_min": 25,
    "auto_brake_counter_value_forward_max": 125,
    "auto_brake_counter_value_reverse_min": 25,
    "auto_brake_counter_value_reverse_max": 125,
    "auto_reverse_counter_value_min": 40,
    "auto_reverse_counter_value_max": 100,
    "brake_disarm_counter_value": 50,
    "blink_counter_value": 17,
    "indicator_idle_time_value": 25,
    "indicator_off_timeout_value": 100,
    "centre_threshold_low": 8,
    "centre_threshold_high": 12,
    "blink_threshold": 30,
    "light_switch_positions": 2,
    "initial_light_switch_position": 0,
    "initial_endpoint_delta": 200,
    "ch3_multi_click_timeout": 15,
    "winch_command_repeat_time": 50,
    "baudrate": 38400,
    "no_signal_timeout": 25,
    "number_of_gears": 2,
    "gearbox_servo_active_time": 50,
    "gearbox_servo_idle_time": 450,
    "servo_pulse_min": 600,
    "servo_pulse_max": 2500,
    "startup_time": 100
  },
  "local_leds": {
    "0": {
      "max_change_per_systick": 0,
      "reduction_percent": 0,
      "weak_light_switch_position0": false,
      "weak_light_switch_position1": false,
      "weak_light_switch_position2": false,
      "weak_light_switch_position3": false,
      "weak_light_switch_position4": false,
      "weak_light_switch_position5": false,
      "weak_light_switch_position6": false,
      "weak_light_switch_position7": false,
      "weak_light_switch_position8": false,
      "weak_tail_light": false,
      "weak_brake_light": false,
      "weak_reversing_light": false,
      "weak_indicator_left": false,
      "weak_indicator_right": false,
      "always_on": 0,
      "light_switch_position0": 0,
      "light_switch_position1": 0,
      "light_switch_position2": 0,
      "light_switch_position3": 0,
      "light_switch_position4": 0,
      "light_switch_position5": 0,
      "light_switch_position6": 0,
      "light_switch_position7": 0,
      "light_switch_position8": 0,
      "tail_light": 0,
      "brake_light": 0,
      "reversing_light": 0,
      "indicator_left": 0,
      "indicator_right": 0
    },
    "1": {
      "max_change_per_systick": 0,
      "reduction_percent": 0,
      "weak_light_switch_position0": false,
      "weak_light_switch_position1": false,
      "weak_light_switch_position2": false,
      "weak_light_switch_position3": false,
      "weak_light_switch_position4": false,
      "weak_light_switch_position5": false,
      "weak_light_switch_position6": false,
      "weak_light_switch_position7": false,
      "weak_light_switch_position8": false,
      "weak_tail_light": false,
      "weak_brake_light": false,
      "weak_reversing_light": false,
      "weak_indicator_left": false,
      "weak_indicator_right": false,
      "always_on": 0,
      "light_switch_position0": 0,
      "light_switch_position1": 0,
      "light_switch_position2": 0,
      "light_switch_position3": 0,
      "light_switch_position4": 0,
      "light_switch_position5": 0,
      "light_switch_position6": 0,
      "light_switch_position7": 0,
      "light_switch_position8": 0,
      "tail_light": 0,
      "brake_light": 0,
      "reversing_light": 0,
      "indicator_left": 0,
      "indicator_right": 0
    },
    "2": {
      "max_change_per_systick": 0,
      "reduction_percent": 0,
      "weak_light_switch_position0": false,
      "weak_light_switch_position1": false,
      "weak_light_switch_position2": false,
      "weak_light_switch_position3": false,
      "weak_light_switch_position4": false,
      "weak_light_switch_position5": false,
      "weak_light_switch_position6": false,
      "weak_light_switch_position7": false,
      "weak_light_switch_position8": false,
      "weak_tail_light": false,
      "weak_brake_light": false,
      "weak_reversing_light": false,
      "weak_indicator_left": false,
      "weak_indicator_right": false,
      "always_on": 0,
      "light_switch_position0": 0,
      "light_switch_position1": 0,
      "light_switch_position2": 0,
      "light_switch_position3": 0,
      "light_switch_position4": 0,
      "light_switch_position5": 0,
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
      "weak_tail_light": false,
      "weak_brake_light": false,
      "weak_reversing_light": false,
      "weak_indicator_left": false,
      "weak_indicator_right": false,
      "always_on": 0,
      "light_switch_position0": 0,
      "light_switch_position1": 0,
      "light_switch_position2": 0,
      "light_switch_position3": 0,
      "light_switch_position4": 0,
      "light_switch_position5": 0,
      "light_switch_position6": 0,
      "light_switch_position7": 0,
      "light_switch_position8": 0,
      "tail_light": 0,
      "brake_light": 0,
      "reversing_light": 0,
      "indicator_left": 0,
      "indicator_right": 0
    },
    "15": {
      "max_change_per_systick": 0,
      "reduction_percent": 0,
      "weak_light_switch_position0": false,
      "weak_light_switch_position1": false,
      "weak_light_switch_position2": false,
      "weak_light_switch_position3": false,
      "weak_light_switch_position4": false,
      "weak_light_switch_position5": false,
      "weak_light_switch_position6": false,
      "weak_light_switch_position7": false,
      "weak_light_switch_position8": false,
      "weak_tail_light": false,
      "weak_brake_light": false,
      "weak_reversing_light": false,
      "weak_indicator_left": false,
      "weak_indicator_right": false,
      "always_on": 0,
      "light_switch_position0": 0,
      "light_switch_position1": 0,
      "light_switch_position2": 0,
      "light_switch_position3": 0,
      "light_switch_position4": 0,
      "light_switch_position5": 0,
      "light_switch_position6": 0,
      "light_switch_position7": 0,
      "light_switch_position8": 0,
      "tail_light": 0,
      "brake_light": 0,
      "reversing_light": 0,
      "indicator_left": 0,
      "indicator_right": 0
    },
    "led_count": 16
  },
  "gamma": {
    "gamma_value": "1.8"
  },
  "light_programs": "// ----------------------------------------------------------------------------\n// Light up the front indicators statically when there is no incoming servo\n// signal\n//\n// If there is no signal for more than five seconds then execute a kind of \n// demo mode\n// ----------------------------------------------------------------------------\nrun when no-signal\n\n// Take over all LEDs\nuse all leds\n\nled main-beam-l = led[14]\nled main-beam-r = led[15]\nled tail-brake-l = led[10]\nled tail-brake-r = led[11]\nled indicator-rear-l = led[9]\nled indicator-rear-r = led[8]\nled reversing-l = led[6]\nled reversing-r = led[7]\n\nvar command\nvar last-command\nvar new-light-switch-position\nvar last-light-switch-position\nvar delay-time\nvar brake-delay-time\nvar indicator-direction\nvar last-indicator-direction\n    \n\n// --------------------------------------------------------------\n    delay-time = 5000\ninitial-loop:\n\tfade all leds stepsize 0\n    all leds = 0%\n\tindicator-rear-l, indicator-rear-r = 100%    \n    sleep 20\n    delay-time -= 20\n    skip if delay-time <= 0\n    goto initial-loop\n\n\tall leds = 0%\n    \n\t// --------------------------------------------------------------\nmain-loop:\n    fade all leds stepsize 0\n\n\t// Random command selection\n\tcommand = random\n    command &= 0x3\n    skip if command != last-command\n    goto main-loop\n    last-command = command\n\t\n    skip if command != 0\n    goto light-switch\n    skip if command != 1\n    goto indicator\n    skip if command != 2\n    goto brake\n    skip if command != 3\n    goto reverse-brake\n    goto main-loop\n    \n// Switch light switch position to random value\nlight-switch:\n\tnew-light-switch-position = random\n    new-light-switch-position &= 0x1\n\tskip if new-light-switch-position != last-light-switch-position\n    goto light-switch\n    last-light-switch-position = new-light-switch-position\n    \n    skip if new-light-switch-position != 0\n    goto lights-off\n\tskip if new-light-switch-position != 1\n    goto lights-main-beam\n    goto light-switch\n\nlights-off:\n\tmain-beam-l, main-beam-r, tail-brake-l, tail-brake-r = 0%\n    goto lights-wait\n    \nlights-main-beam:\n\tmain-beam-l, main-beam-r = 100%\n    tail-brake-l, tail-brake-r = 25%\n    //goto lights-wait\n\nlights-wait:\n    delay-time = random\n    delay-time &= 0x7ff\n    delay-time += 1000\n    sleep delay-time\n\tgoto main-loop\n\n// Turn indicator in random direction (or hazard), for a random time\nindicator:\n\tindicator-direction = random\n    indicator-direction &= 0x3\n\tskip if indicator-direction != last-indicator-direction\n    goto indicator\n    last-indicator-direction = indicator-direction\n\n\t// An indicator cycle is 640 ms. We want the indicators on for 2..10s\n    // so we create a random value beteen 3 and 16 (* 640 ms)\n\tdelay-time = random\t\t\t \n    delay-time &= 0xf\n    skip if delay-time < 13\n    delay-time -= 13\n    delay-time += 3\n\n    skip if indicator-direction != 0\n    goto indicator-left\n    skip if indicator-direction != 1\n    goto indicator-right\n    skip if indicator-direction != 2\n    goto hazard-active\n    goto indicator\n    \nindicator-left:\n\tindicator-rear-l = 100%\n\tsleep 320\n\tindicator-rear-l = 0%\n\tsleep 320\n\tdelay-time -= 1\n    skip if delay-time <= 0\n    goto indicator-left\n\tgoto main-loop\n    \nindicator-right:\n\tindicator-rear-r = 100%\n\tsleep 320\n\tindicator-rear-r = 0%\n\tsleep 320\n\tdelay-time -= 1\n    skip if delay-time <= 0\n    goto indicator-right\n\tgoto main-loop\n\nhazard-active:\n\tindicator-rear-r, indicator-rear-l = 100%\n\tsleep 320\n\tindicator-rear-r, indicator-rear-l = 0%\n\tsleep 320\n\tdelay-time -= 1\n    skip if delay-time <= 0\n    goto hazard-active\n\tgoto main-loop\n\n\n//\tTurn brake lights on for a random time\nbrake:\n\ttail-brake-l, tail-brake-r = 100%\n    delay-time = random\n    delay-time &= 0x1fff\n    skip if delay-time < 4000\n    delay-time -= 4000\n    delay-time += 500\n    sleep delay-time\n  \ttail-brake-l, tail-brake-r = 0%\n\tskip if new-light-switch-position != 0\n    goto main-loop\n\ttail-brake-l, tail-brake-r = 25%\n\tgoto main-loop\n\n\n//  Turn reverse on for a random time, then brake for random time\nreverse-brake:\n\treversing-l, reversing-r = 100%\n    delay-time = random\n    delay-time &= 0x7ff\n    delay-time += 500\n    sleep delay-time\n\n\ttail-brake-l, tail-brake-r = 100%\n    delay-time = random\n    delay-time &= 0x1f\n    brake-delay-time = random\n    brake-delay-time &= 0x1f\n    \nreverse-brake-loop:\n\tsleep 100\n    skip if delay-time != 0\n    goto check-brake\n\tdelay-time -= 1\n    skip if delay-time == 0\n    goto check-brake\n  \treversing-l, reversing-r = 0%\n    \ncheck-brake:    \n    skip if brake-delay-time != 0\n    goto check-if-done\n\tbrake-delay-time -= 1\n    skip if brake-delay-time == 0\n    goto check-if-done\n  \ttail-brake-l, tail-brake-r = 0%\n\tskip if new-light-switch-position != 0\n    goto check-if-done\n\ttail-brake-l, tail-brake-r = 25%\n    \ncheck-if-done:    \n    skip if delay-time == 0\n    goto reverse-brake-loop\n    skip if brake-delay-time == 0\n    goto reverse-brake-loop\n  \treversing-l, reversing-r = 0%\n    goto lights-wait\n\nend\n\n// ----------------------------------------------------------------------------\n// Light up the incidcators (rear) while the light controller is initializing.\n// ----------------------------------------------------------------------------\nrun when initializing\n\nuse all leds\nled indicator-l = led[9]\nled indicator-r = led[8]\n\n\n\tlight-switch-position = 1\t// Turn on the car lights by default\n\nloop:\n    fade all leds stepsize 0\n    all leds = 0%\n    indicator-l, indicator-r = 100%\n    sleep 0\n    goto loop\n\nend\n\n\n// ----------------------------------------------------------------------------\n// Steering an throttle reversing setup\n//\n// This program runs after 7 CH3-clicks. The user is expected to turn the\n// steering wheel to the same direction as the indicators are lighting up,\n// and push the throttle forward.\n//\n// Therefore we turn the left indicators on until we detect the user having\n// given significant steering input (reversing-setup-steering goes off).\n// We also turn the high beam on until we detect significant throttle input\n// (reversing-setup-throttle goes off).\n//\n// Once both are off the light controller lights resume their normal function\n// as the condition for running this program is \"false\".\n// ----------------------------------------------------------------------------\nrun when reversing-setup-steering or reversing-setup-throttle\n\nuse all leds\nled main-beam-l = led[14]\nled main-beam-r = led[15]\nled indicator-l = led[8]\nled indicator-r = led[9]\n\nloop:\n    sleep 0\n\n    fade all leds stepsize 0\n\n    // Turn all lights off, then indicators or high beam on selectivly.\n    // This won't cause any flicker as the light output is only executed\n    // when a light program executes a \"sleep\" statement (or at the end of\n    // a light program).\n    all leds = 0%\n\n    skip if is reversing-setup-steering         // Steering setup?\n    goto not_steering                           // No: check throttle\n    indicator-l, indicator-l = 100%   \t\t\t// Yes: light up the indicators\n\nnot_steering:\n    skip if is reversing-setup-throttle         // Throttle setup?\n    goto loop                                   // No: start over\n    main-beam-l, main-beam-r = 100%             // Yes: light up main beam\n    goto loop\n\nend\n\n\n// ----------------------------------------------------------------------------\n// Servo output endpoint setup\n//\n// This program runs after 8 CH3-clicks. The user can now use the steering\n// wheel on the transmitter to directly drive the servo output (i.e. the\n// servo output behaves like the servo would be connected to the steering\n// output of the receiver).\n//\n// The user can now setup what he considers \"left\" endpoint (or gear 1 if it\n// is a gearbox servo). Then one CH3-click switches to \"center\" (or gear 2).\n// Another CH3-click switches to \"right\" (or gear 3). A final CH3-click\n// ends the procedure, saves the endpoints and resumes normal operation.\n//\n// At any point in time during the setup two or more clicks cancel the servo\n// output setup and restore the original endpoints.\n// ----------------------------------------------------------------------------\n\n\n// Note: \"or\" between the conditions is optional, same meaning with or without\nrun when servo-output-setup-centre servo-output-setup-left servo-output-setup-right\n\nuse all leds\nled indicator-l = led[9]\nled indicator-r = led[8]\n\nloop:\n    sleep 0\n\n    fade all leds stepsize 0\n    all leds = 0%\n\n    skip if not servo-output-setup-left\n    goto left\n    skip if not servo-output-setup-right\n    goto right\n    // If it is neither left nor right, it must be centre...\n    // Otherwise the program would not be run in the first place, see RUN WHEN\n    // above!\n\n    // Centre setup: light up all four indicators\ncentre:\n    indicator-l, indicator-r = 100%\n    goto loop\n\n    // Left setup: light up all indicators on the left side\nleft:\n    indicator-l = 100%\n    goto loop\n\n    // Right setup: light up all indicators on the right side\nright:\n    indicator-r = 100%\n    goto loop\n\nend\n"
}
