laneboysrc/rc-light-controller/mk4-tlc5940-lpc812/firmware/globals.h

#ifndef __GLOBALS_H
#define __GLOBALS_H

#include <stdint.h>
#include <stdbool.h>


#define STDOUT ((void *) 1)
#define STDOUT_DEBUG ((void *) 2)


#define CONFIG_VERSION 2
#define __SYSTICK_IN_MS 20


// Suppress unused parameter or variable warning
#ifndef UNUSED
#define UNUSED(x) ((void)(x))
#endif

#define OFF false
#define ON true

// The ROM_MAGIC marker is used to identify the location of ROM constants when
// parsing a light controller binary by an external tool
#define ROM_MAGIC 0x6372424c                // LBrc (LANE Boys RC) in little endian

#define NUMBER_OF_CHANNELS 8
#define ST 0
#define TH 1
#define AUX 2
#define AUX2 3
#define AUX3 4
#define AUX4 5
#define AUX5 6
#define AUX6 7

// Percentage that an AUX value has to change before causing a trigger
#define AUX_HYSTERESIS 10

// Number of positions of our virtual light switch. Includes the "off"
// position 0.
// NOTE: if you change this value you need to adjust CAR_LIGHT_FUNCTION_T
// accordingly!
#define LIGHT_SWITCH_POSITIONS 9

#define MAX_LIGHT_PROGRAMS 25
#define MAX_LIGHT_PROGRAM_VARIABLES 100

// Convenience functions for min/max
#define MIN(x, y) ((x) < (y) ? x : (y))
#define MAX(x, y) ((x) > (y) ? x : (y))


// Opcodes for light programs
#define OPCODE_GOTO             0x01    // GOTO instruction offset

#define OPCODE_SET              0x02    // LED start..stop = var
#define OPCODE_SET_I            0x03    // LED start..stop = uint8_t immediate

#define OPCODE_FADE             0x04    // FADE start..stop with var
#define OPCODE_FADE_I           0x05    // FADE start..stop with uint8_t immediate

#define OPCODE_SLEEP            0x06    // SLEEP type, id (ms)
#define OPCODE_SLEEP_I          0x07    // SLEEP immediate (ms)

#define OPCODE_ASSIGN           0x10    // VAR = type, id
#define OPCODE_ASSIGN_I         0x11    // VAR = immediate

#define OPCODE_ADD              0x12    // VAR += type, id
#define OPCODE_ADD_I            0x13    // VAR += immediate

#define OPCODE_SUBTRACT         0x14    // VAR -= type, id
#define OPCODE_SUBTRACT_I       0x15    // VAR -= immediate

#define OPCODE_MULTIPLY         0x16    // VAR *= type, id
#define OPCODE_MULTIPLY_I       0x17    // VAR *= immediate

#define OPCODE_DIVIDE           0x18    // VAR /= type, id
#define OPCODE_DIVIDE_I         0x19    // VAR /= immediate

#define OPCODE_AND              0x1a    // VAR &= type, id
#define OPCODE_AND_I            0x1b    // VAR &= immediate

#define OPCODE_OR               0x1c    // VAR |= type, id
#define OPCODE_OR_I             0x1d    // VAR |= immediate

#define OPCODE_XOR              0x1e    // VAR ^= type, id
#define OPCODE_XOR_I            0x1f    // VAR ^= immediate

#define OPCODE_MOD              0x38    // VAR %= type, id
#define OPCODE_MOD_I            0x39    // VAR %= immediate


#define FIRST_SKIP_IF_OPCODE    0x20
#define OPCODE_SKIP_IF_EQ_V     0x20    // var == type, id
#define OPCODE_SKIP_IF_EQ_VI    0x21    // var == immediate
#define OPCODE_SKIP_IF_EQ_L     0x22    // led == type, id
#define OPCODE_SKIP_IF_EQ_LI    0x23    // led == immediate

#define OPCODE_SKIP_IF_NE_V     0x24    // var != type, id
#define OPCODE_SKIP_IF_NE_VI    0x25    // var != immediate
#define OPCODE_SKIP_IF_NE_L     0x26    // led != type, id
#define OPCODE_SKIP_IF_NE_LI    0x27    // led != immediate

#define OPCODE_SKIP_IF_GE_V     0x28    // var >= type, id
#define OPCODE_SKIP_IF_GE_VI    0x29    // var >= immediate
#define OPCODE_SKIP_IF_GE_L     0x2a    // led >= type, id
#define OPCODE_SKIP_IF_GE_LI    0x2b    // led >= immediate

#define OPCODE_SKIP_IF_GT_V     0x2c    // var > type, id
#define OPCODE_SKIP_IF_GT_VI    0x2d    // var > immediate
#define OPCODE_SKIP_IF_GT_L     0x2e    // led > type, id
#define OPCODE_SKIP_IF_GT_LI    0x2f    // led > immediate

#define OPCODE_SKIP_IF_LE_V     0x30    // var >= type, id
#define OPCODE_SKIP_IF_LE_VI    0x31    // var >= immediate
#define OPCODE_SKIP_IF_LE_L     0x32    // led >= type, id
#define OPCODE_SKIP_IF_LE_LI    0x33    // led >= immediate

#define OPCODE_SKIP_IF_LT_V     0x34    // var > type, id
#define OPCODE_SKIP_IF_LT_VI    0x35    // var > immediate
#define OPCODE_SKIP_IF_LT_L     0x36    // led > type, id
#define OPCODE_SKIP_IF_LT_LI    0x37    // led > immediate
#define LAST_SKIP_IF_OPCODE     0x37

#define OPCODE_ABS              0x40    // var = |type, id|
#define OPCODE_ABS_I            0x41    // var = |immediate|

#define OPCODE_SKIP_IF_ANY      0x60    // 011 + 29 bits run_state! 0x60 .. 0x7f
#define OPCODE_SKIP_IF_ALL      0x80    // 100 + 29 bits run_state! 0x80 .. 0x9f
#define OPCODE_SKIP_IF_NONE     0xA0    // 101 + 29 bits run_state! 0xa0 .. 0xbf

#define OPCODE_END_OF_PROGRAM   0xfe
#define OPCODE_END_OF_PROGRAMS  0xff


#define PARAMETER_TYPE_VARIABLE 0
#define PARAMETER_TYPE_LED 1
#define PARAMETER_TYPE_RANDOM 2
// #define PARAMETER_TYPE_STEERING 3
// #define PARAMETER_TYPE_THROTTLE 4
// Note: not used from version 24 onwards, replaced with global variable!
// #define PARAMETER_TYPE_GEAR 5
// #define PARAMETER_TYPE_AUX 6
// #define PARAMETER_TYPE_AUX2 7
// #define PARAMETER_TYPE_AUX3 8


// Offset of special position within every light program
#define PRIORITY_STATE_OFFSET 0
#define RUN_STATE_OFFSET 1
#define LEDS_USED_OFFSET 2
#define FIRST_OPCODE_OFFSET 3


#define LED_USED(x) (1 << x)
#define START_LED(x) (x << 16)
#define STOP_LED(x) (x << 8)

typedef uint8_t LED_T;

// ****************************************************************************
typedef enum {
    // These run conditions align with LIGHT_PROGRAM_CAR_STATE_T so that in the
    // implementation we can build one and copy the data to the other one
    // before extending them with the unique values

    RUN_WHEN_LIGHT_SWITCH_POSITION   = (1 << 0),     // Bits 0..8
    RUN_WHEN_LIGHT_SWITCH_POSITION_1 = (1 << 1),
    RUN_WHEN_LIGHT_SWITCH_POSITION_2 = (1 << 2),
    RUN_WHEN_LIGHT_SWITCH_POSITION_3 = (1 << 3),
    RUN_WHEN_LIGHT_SWITCH_POSITION_4 = (1 << 4),
    RUN_WHEN_LIGHT_SWITCH_POSITION_5 = (1 << 5),
    RUN_WHEN_LIGHT_SWITCH_POSITION_6 = (1 << 6),
    RUN_WHEN_LIGHT_SWITCH_POSITION_7 = (1 << 7),
    RUN_WHEN_LIGHT_SWITCH_POSITION_8 = (1 << 8),

    RUN_WHEN_NEUTRAL                 = (1 << 9),
    RUN_WHEN_FORWARD                 = (1 << 10),
    RUN_WHEN_REVERSING               = (1 << 11),
    RUN_WHEN_BRAKING                 = (1 << 12),

    RUN_WHEN_INDICATOR_LEFT          = (1 << 13),
    RUN_WHEN_INDICATOR_RIGHT         = (1 << 14),
    RUN_WHEN_HAZARD                  = (1 << 15),
    RUN_WHEN_BLINK_FLAG              = (1 << 16),
    RUN_WHEN_BLINK_LEFT              = (1 << 17),
    RUN_WHEN_BLINK_RIGHT             = (1 << 18),

    // RUN_WHEN_WINCH_DISABLERD         = (1 << 19),
    // RUN_WHEN_WINCH_IDLE              = (1 << 20),
    // RUN_WHEN_WINCH_IN                = (1 << 21),
    // RUN_WHEN_WINCH_OUT               = (1 << 22),

    // End of defines that are shared with LIGHT_PROGRAM_CAR_STATE_T

    RUN_WHEN_PROGRAM_STATE_0         = (1 << 24),
    RUN_WHEN_PROGRAM_STATE_1         = (1 << 25),
    RUN_WHEN_PROGRAM_STATE_2         = (1 << 26),
    RUN_WHEN_PROGRAM_STATE_3         = (1 << 27),
    RUN_WHEN_PROGRAM_STATE_4         = (1 << 28),

    // RUN_ALWAYS                    = (1 << 31)
    // Enums are of type integer, so 1<<31 isn't an allowed value as it is
    // larger than INT_MAX. Starting with gcc version 6 this raises a warning
    // when compiling.
    // Since we are not actually using the enum but uint32_t for the variable
    // that holds the state, we can simply use a define as work-around.
    // Maybe cleaner would be to switch everything to #defines...
    #define RUN_ALWAYS                 (1 << 31)

} LIGHT_PROGRAM_RUN_STATE_T;


// ****************************************************************************
typedef enum {
    RUN_WHEN_NORMAL_OPERATION           = 0,
    RUN_WHEN_NO_SIGNAL                  = (1 << 0),
    RUN_WHEN_INITIALIZING               = (1 << 1),
    RUN_WHEN_SERVO_OUTPUT_SETUP_CENTRE  = (1 << 2),
    RUN_WHEN_SERVO_OUTPUT_SETUP_LEFT    = (1 << 3),
    RUN_WHEN_SERVO_OUTPUT_SETUP_RIGHT   = (1 << 4),
    RUN_WHEN_REVERSING_SETUP_STEERING   = (1 << 5),
    RUN_WHEN_REVERSING_SETUP_THROTTLE   = (1 << 6),
    RUN_WHEN_GEAR_CHANGED               = (1 << 7),
    RUN_WHEN_SHELF_QUEEN_MODE           = (1 << 8),
} LIGHT_PROGRAM_PRIORITY_STATE_T;


// ****************************************************************************
typedef enum {
    // These run conditions align with LIGHT_PROGRAM_RUN_STATE_T so that in the
    // implementation we can build one and copy the data to the other one
    // before extending them with the unique values
    CAR_STATE_LIGHT_SWITCH_POSITION     = (1 << 0),     // Bits 0..8
    CAR_STATE_LIGHT_SWITCH_POSITION_1   = (1 << 1),
    CAR_STATE_LIGHT_SWITCH_POSITION_2   = (1 << 2),
    CAR_STATE_LIGHT_SWITCH_POSITION_3   = (1 << 3),
    CAR_STATE_LIGHT_SWITCH_POSITION_4   = (1 << 4),
    CAR_STATE_LIGHT_SWITCH_POSITION_5   = (1 << 5),
    CAR_STATE_LIGHT_SWITCH_POSITION_6   = (1 << 6),
    CAR_STATE_LIGHT_SWITCH_POSITION_7   = (1 << 7),
    CAR_STATE_LIGHT_SWITCH_POSITION_8   = (1 << 8),

    CAR_STATE_NEUTRAL                   = (1 << 9),
    CAR_STATE_FORWARD                   = (1 << 10),
    CAR_STATE_REVERSING                 = (1 << 11),
    CAR_STATE_BRAKING                   = (1 << 12),

    CAR_STATE_INDICATOR_LEFT            = (1 << 13),
    CAR_STATE_INDICATOR_RIGHT           = (1 << 14),
    CAR_STATE_HAZARD                    = (1 << 15),
    CAR_STATE_BLINK_FLAG                = (1 << 16),
    CAR_STATE_BLINK_LEFT                = (1 << 17),
    CAR_STATE_BLINK_RIGHT               = (1 << 18),

    // CAR_STATE_WINCH_DISABLERD           = (1 << 19),
    // CAR_STATE_WINCH_IDLE                = (1 << 20),
    // CAR_STATE_WINCH_IN                  = (1 << 21),
    // CAR_STATE_WINCH_OUT                 = (1 << 22),

    // End of defines that are shared with LIGHT_PROGRAM_RUN_STATE_T

    // 1 bit still free ...

    CAR_STATE_SERVO_OUTPUT_SETUP_CENTRE = (1 << 24),
    CAR_STATE_SERVO_OUTPUT_SETUP_LEFT   = (1 << 25),
    CAR_STATE_SERVO_OUTPUT_SETUP_RIGHT  = (1 << 26),
    CAR_STATE_REVERSING_SETUP_STEERING  = (1 << 27),
    CAR_STATE_REVERSING_SETUP_THROTTLE  = (1 << 28),
} LIGHT_PROGRAM_CAR_STATE_T;


// ****************************************************************************
typedef enum {
    // By specifying this unused value we force the enmeration to fit in a
    // uint16_t
    EMPTY = 0xffff,

    CONFIG_SECTION = 0x01,
    GAMMA_TABLE = 0x02,
    LOCAL_LEDS = 0x10,
    SLAVE_LEDS = 0x20,
    LIGHT_PROGRAMS = 0x30
} ROM_SECTION_T;


// ****************************************************************************
typedef struct {
    uint32_t magic_value;
    ROM_SECTION_T type;
    uint16_t version;
} MAGIC_T;


// ****************************************************************************
typedef struct {
    MAGIC_T magic;
    char gamma_value[4];
    uint8_t gamma_table[256];
} GAMMA_TABLE_T;


// ****************************************************************************
typedef struct {
    MAGIC_T magic;
    // Important: these need to be declared volatile as otherwise the compiler
    // may use the compile-time values (= no light program) to optimize code
    // away, and then light programs added by the configurator don't work
    // anymore!
    volatile uint32_t number_of_programs;
    volatile uint32_t programs[1];
} LIGHT_PROGRAMS_T;


// ****************************************************************************
typedef struct {
    uint16_t left;
    uint16_t centre;
    uint16_t right;
} SERVO_ENDPOINTS_T;


// ****************************************************************************
typedef struct {
    uint32_t raw_data;
    SERVO_ENDPOINTS_T endpoint;
    int16_t normalized;
    uint16_t absolute;
    bool reversed;
    bool auto_endpoint;
} CHANNEL_T;


// ****************************************************************************
typedef enum {
    GEAR_1 = 1,
    GEAR_2 = 2,
    GEAR_3 = 3
} GEAR_T;


// ****************************************************************************
typedef enum {
    SERVO_OUTPUT_SETUP_OFF = 0,
    SERVO_OUTPUT_SETUP_CENTRE = 0x01,
    SERVO_OUTPUT_SETUP_LEFT = 0x02,
    SERVO_OUTPUT_SETUP_RIGHT = 0x04
} SERVO_OUTPUT_T;


// ****************************************************************************
typedef enum {
    REVERSING_SETUP_OFF = 0,
    REVERSING_SETUP_STEERING = 0x01,
    REVERSING_SETUP_THROTTLE = 0x02,
} REVERSING_SETUP_T;


// ****************************************************************************
// typedef enum {
//     WINCH_DISABLED = 0,
//     WINCH_IDLE = 0x01,
//     WINCH_IN = 0x02,
//     WINCH_OUT = 0x04
// } WINCH_T;


// ****************************************************************************
typedef enum {
    TWO_POSITION = 0,
    TWO_POSITION_UP_DOWN = 1,
    MOMENTARY = 2,
    THREE_POSITION = 3,
    ANALOG = 4
} AUX_TYPE_T;


// ****************************************************************************
typedef enum {
    NOT_USED = 0,
    MULTI_FUNCTION = 1,
    GEARBOX = 2,
    // WINCH = 3,
    SERVO = 4,
    INDICATORS = 5,
    HAZARD = 6,
    LIGHT_SWITCH = 7,
    DISABLE_OUTPUTS = 8,
} AUX_FUNCTION_T;


// ****************************************************************************
// IMPORTANT: the order of the GLOBAL_FLAGS_T structure has been "optimized"
// manually for minimal code side. Moving elements around or changing the
// "alignment" of bit fields can add more than 68 Bytes in code!
//
typedef struct {
    unsigned int servo_output_setup : 3;

    unsigned int systick : 1;               // Set for one mainloop every 20 ms
    unsigned int new_channel_data : 1;      // Set for one mainloop every time servo pulses were received

    unsigned int initializing : 1;
    unsigned int no_signal : 1;

    unsigned int blink_flag : 1;            // Toggles with 1.5 Hz
    unsigned int blink_hazard : 1;          // Hazard lights active
    unsigned int blink_indicator_left : 1;  // Left indicator active
    unsigned int blink_indicator_right : 1; // Right indicator active

    unsigned int forward : 1;               // Set when the car is driving forward
    unsigned int braking : 1;               // Set when the brakes are enganged
    unsigned int reversing : 1;             // Set when the car is reversing

    unsigned int reserved0 : 2;

    unsigned int shelf_queen_mode : 1;      // Set when car driving is simulated
    unsigned int outputs_disabled : 1;      // Set when all LED outputs should be disabled
    unsigned int switched_outputs : 1;      // Set when this is a light controller with 9 switched outputs (Mk4S)

    unsigned int gear_changed : 1;          // Set for one mainloop when a new gear was selected
    unsigned int gear : 2;
    unsigned int gear_change_requested : 1; // Set until the next mainloop to synchronize gear_changed event

    unsigned int reserved1 : 1;

    unsigned int reversing_setup : 2;
} GLOBAL_FLAGS_T;


// ****************************************************************************
typedef enum {
    MASTER_WITH_SERVO_READER,
    MASTER_WITH_UART_READER,
    DISABLED,                   // MASTER_WITH_CPPM_READER => NOT SUPPORTED ANYMORE!
    SLAVE,
    STAND_ALONE,
    MASTER_WITH_IBUS_READER,
    MASTER_WITH_SBUS_READER,
} MASTER_MODE_T;


// ****************************************************************************
// If ESC_FORWARD_BRAKE_REVERSE, the user has to go for
// brake, then neutral, before reverse engages.
// If ESC_FORWARD_BRAKE_REVERSE_TIMEOUT, reverse can be engaged if the user
// stays in neutral for a few seconds.
//
// Tamiya ESC are of type ESC_FORWARD_BRAKE_REVERSE.
// The China ESC and HPI SC-15WP are of type ESC_FORWARD_BRAKE_REVERSE_TIMEOUT.
typedef enum {
    ESC_FORWARD_BRAKE_REVERSE_TIMEOUT,
    ESC_FORWARD_BRAKE_REVERSE,
    ESC_FORWARD_REVERSE,
    ESC_FORWARD_BRAKE
} ESC_MODE_T;


// ****************************************************************************
typedef struct {
    MAGIC_T magic;

    uint8_t firmware_version;

    MASTER_MODE_T mode;
    ESC_MODE_T esc_mode;

    struct {
        // If mode is MASTER_WITH_SERVO_READER  then all flags are mutually
        // exculsive.
        // If mode is MASTER_WITH_UART_READER or MASTER_WITH_CPPM_INPUT then
        // there can be one UART output (slave, preprocessor or winch) and one
        // servo output (steering wheel or gearbox servo; or switched light
        // output)
        unsigned int slave_output : 1;
        unsigned int preprocessor_output : 1;
        // unsigned int winch_output : 1;
        unsigned int reserved1 : 1;     // previously winch output
        unsigned int steering_wheel_servo_output : 1;
        unsigned int gearbox_servo_output : 1;

        unsigned int reserved0 : 1;

        unsigned int ch3_is_local_switch : 1;
        unsigned int ch3_is_momentary : 1;

        unsigned int auto_brake_lights_forward_enabled : 1;
        unsigned int auto_brake_lights_reverse_enabled : 1;

        unsigned int ch3_is_two_button : 1;

        // Channel reversing via the configurator. Added in config v2 firmware v35
        unsigned int reverse_st : 1;
        unsigned int reverse_th : 1;
        unsigned int reverse_aux : 1;
        unsigned int reverse_aux2 : 1;
        unsigned int reverse_aux3 : 1;
    } flags;

    uint16_t auto_brake_counter_value_forward_min;
    uint16_t auto_brake_counter_value_forward_max;
    uint16_t auto_brake_counter_value_reverse_min;
    uint16_t auto_brake_counter_value_reverse_max;

    uint16_t auto_reverse_counter_value_min;
    uint16_t auto_reverse_counter_value_max;

    uint16_t brake_disarm_counter_value;

    uint16_t blink_counter_value;
    uint16_t indicator_idle_time_value;
    uint16_t indicator_off_timeout_value;

    // Centre threshold defines a range where we consider the servo being
    // centred. In order to prevent "flickering" especially for the brake and
    // reverse light the CENTRE_THRESHOLD_HIGH and CENTRE_THRESHOLD_LOW provide
    // a hysteresis that we apply to the throttle when processing drive_mode.
    uint16_t centre_threshold_low;
    uint16_t centre_threshold_high;
    uint16_t blink_threshold;

    uint16_t light_switch_positions;
    uint16_t initial_light_switch_position;
    uint16_t initial_endpoint_delta;
    uint16_t ch3_multi_click_timeout;

    // uint16_t winch_command_repeat_time;
    uint16_t reserved2;     // previously used for the winch

    uint32_t baudrate;
    uint16_t no_signal_timeout;
    uint16_t number_of_gears;
    uint16_t gearbox_servo_active_time;
    uint16_t gearbox_servo_idle_time;

    uint16_t servo_pulse_min;
    uint16_t servo_pulse_max;

    uint16_t startup_time;

    // -------------------------------------------------------------------
    // From here-on down are settings have been added in config version 2!
    // -------------------------------------------------------------------

    struct {
        // Enables handling of two additional AUX channels
        unsigned int multi_aux : 1;

        // Enable shelf queen mode where driving action is simulated if there
        // is no receiver signal for more than 5 seconds
        unsigned int shelf_queen_mode : 1;

        // Set to 1 to use proper US style combined indicator/tail/brake,
        // set to 0 for the old mode we used in our XR311
        unsigned int us_style_combined_lights :1;

        // Set to 1 when the gearbox should be controlled through light
        // programs only and not 1/2 clicks.
        // Only in effect when gearbox_servo_output is enabled.
        unsigned int gearbox_light_program_control :1;

        // Set to 1 when the servo can be directly controlled from light
        // programs, range -100 / 0 / +100
        unsigned int light_program_servo_output :1;

        // Set to 1 when the indicators should also engage while the car is
        // driving. By default (flag is 0) they only engage if both throttle
        // and steering is 0 for a certain time.
        unsigned int indicators_while_driving :1;

        // Convenience flags that indicate which pin should have what function
        // to reduce complexity and code size
        // For pre-processor reader, uart_rx_on_st would be set; but for
        // servo reader it would be cleared.
        // Some flags are mutually exclusive, i.e. only one of uart_tx_on_th
        // and servo_on_th can be set.
        unsigned int uart_rx_on_st :1;
        unsigned int uart_tx_on_th :1;
        unsigned int uart_tx_on_out :1;
        unsigned int servo_on_th :1;
        unsigned int servo_on_out :1;

        // Set when the UART output is not used and therefore available for
        // human-readable diagnostics messages.
        unsigned int uart_diagnostics_enabled :1;

        // Convenience flag to save code space. Set when any of the servo
        // output functions is enabled (including direct servo control on
        // multi-aux)
        unsigned int servo_output_enabled :1;

        // If set, require one more click than usual; This implies that 1 click
        // has no function (except abort winching!).
        // Use-case: Traxxas TRX4 where the gearbox and light controller share
        // one channel. Then the user can switch "slow" to change the gear,
        // and fast (2 or more clicks) to operate the lights.
        unsigned int require_extra_click : 1;

        // By default (prefer_all_lights_off = 0) 3-clicks on AUX switch to
        // the highest used light switch position.
        // If we are already in the highest used light switch position then
        // 3-clicks switch to light switch position 0
        //
        // When prefer_all_lights_off is set, then 3-cicks switches to
        // light switch position 0.
        // If we are already at light switch position 0, then 3-clicks switches
        // to the highest used light switch position.
        //
        // This feature was added as per customer request
        unsigned int prefer_all_lights_off : 1;

        // Invert output OUT15S
        // This was requested so that the light controller can control an
        // external DC/DC converter with an enable function, hooked up to
        // a light bar.
        unsigned int invert_out15s : 1;

        // All of flags2 used up!
        // unsigned int reserved0 : 0;
    } flags2;

    // Dark phase of the indicator. The blink_counter_value from config version
    // 1 determines the bright phase length.
    uint16_t blink_counter_value_dark;

    AUX_TYPE_T aux_type;
    AUX_FUNCTION_T aux_function;

    AUX_TYPE_T aux2_type;
    AUX_FUNCTION_T aux2_function;

    AUX_TYPE_T aux3_type;
    AUX_FUNCTION_T aux3_function;

    int8_t light_switch_centers[9];
    int8_t light_switch_hysteresis;

    // Advanced config for the threshold for the AUX 2-position and
    // 3-position functions
    int8_t aux_centre_threshold_low;
    int8_t aux_centre_threshold_high;
    int8_t aux_left_centre_threshold_low;
    int8_t aux_left_centre_threshold_high;
    int8_t aux_centre_right_threshold_low;
    int8_t aux_centre_right_threshold_high;

    // Brightness value for LED table driven diagnostics
    LED_T diagnostics_brightness;
    // Mask to indicate which diagnostics functions (no-signal, initializing, ...)
    // are actually used in the table. The order is as defined for
    // LIGHT_PROGRAM_PRIORITY_STATE_T
    uint8_t diagnostics_mask;

    // This variable allows to move the AUX channels to different channels
    // on i-Bus amd SBUS. By default AUX maps to CH3, AUX2 to CH4, AUX3 to CH5.
    // When setting this variable for example to "2", then AUX maps to CH5,
    // AUX2 to CH6 and AUX3 to CH7.
    //
    // The allowed value range is 0..9 (CH3..CH12)
    // Going beyond channel 14 would require bit-mangling and would add a lot of
    // code.
    uint8_t aux_channel_offset;

    // v60: add configuratble servo outputs defaults
    // Based on user request where the default 1-2ms where not sufficient
    uint16_t servo_out_pulse_left;
    uint16_t servo_out_pulse_centre;
    uint16_t servo_out_pulse_right;

} LIGHT_CONTROLLER_CONFIG_T;


// ****************************************************************************
// Definitions for the various light configuration structures


typedef struct {    // 4-bytes packed (2 bits free)
    // Simulation of incandescent lights
    uint8_t max_change_per_systick;

    // Simulation of a weak ground connection
    uint8_t reduction_percent;
    unsigned int light_switch_position_0 : 1;
    unsigned int light_switch_position_1 : 1;
    unsigned int light_switch_position_2 : 1;
    unsigned int light_switch_position_3 : 1;
    unsigned int light_switch_position_4 : 1;
    unsigned int light_switch_position_5 : 1;
    unsigned int light_switch_position_6 : 1;
    unsigned int light_switch_position_7 : 1;
    unsigned int light_switch_position_8 : 1;
    unsigned int tail_light : 1;
    unsigned int brake_light : 1;
    unsigned int reversing_light : 1;
    unsigned int indicator_left : 1;
    unsigned int indicator_right : 1;
} LIGHT_FEATURE_T;

// For standard car light functions we have an array of values, one per LED,
// where each entry corresponds to one light funciton. The user can assign
// multiple functions to a single LED (such as brake and tail light function)
// and the software will "mix" the final color value.

typedef struct {    // 20-bytes packed (all used up)
    LIGHT_FEATURE_T features;

    LED_T always_on;
    LED_T light_switch_position[LIGHT_SWITCH_POSITIONS];
    LED_T tail_light;
    LED_T brake_light;
    LED_T reversing_light;
    LED_T indicator_left;
    LED_T indicator_right;

    // Diagnostics is a bit field with the same order as defined in
    // LIGHT_PROGRAM_PRIORITY_STATE_T, so that we can use those to test against.
    //     unsigned int no_signal : 1;
    //     unsigned int initializing : 1;
    //     unsigned int servo_output_setup_centre : 1;
    //     unsigned int servo_output_setup_left : 1;
    //     unsigned int servo_output_setup_right : 1;
    //     unsigned int rerversing_setup_steering : 1;
    //     unsigned int rerversing_setup_throttle : 1;
    //
    uint8_t diagnostics;

} CAR_LIGHT_T;


typedef struct {
    MAGIC_T magic;
    uint8_t led_count;  // Number of actually used LEDs

    // Pointer to the first element in an array of lights.
    const CAR_LIGHT_T *car_lights;
} CAR_LIGHT_ARRAY_T;


// ****************************************************************************
// The entropy variable is incremented every mainloop. It can therefore serve
// as a random value in practical RC car application,
// Certainly not suitable for secure implementations...
extern uint32_t entropy;

extern const LIGHT_CONTROLLER_CONFIG_T config;
extern const CAR_LIGHT_ARRAY_T local_leds;
extern const CAR_LIGHT_ARRAY_T slave_leds;
extern const GAMMA_TABLE_T gamma_table;
extern const LIGHT_PROGRAMS_T light_programs;

extern GLOBAL_FLAGS_T global_flags;
extern CHANNEL_T channel[NUMBER_OF_CHANNELS];
extern SERVO_ENDPOINTS_T servo_output_endpoint;


// ****************************************************************************
// Globally accessible functions from various modules

void load_persistent_storage(void);
void write_persistent_storage(void);

void init_servo_reader(void);
void read_all_servo_channels(void);

bool ibus_reader_get_new_channels(uint32_t *out);
bool sbus_reader_get_new_channels(uint32_t *out);

void read_preprocessor(void);


void process_aux(void);

void init_drive_mode(void);
void process_drive_mode(void);
void throttle_neutral(void);

void process_indicators(void);
void set_hazard_lights(bool state);
void set_blink_off(void);
void set_blink_left(void);
void set_blink_right(void);


void init_servo_output(void);
void process_servo_output(void);
void servo_output_setup_action(uint8_t ch3_clicks);
void gearbox_action(uint8_t ch3_clicks);
void set_gear(uint8_t new_gear);
void set_servo_pulse(uint16_t value);
void set_servo_position(int16_t value);
int8_t get_servo_position(void);

// void process_winch(void);
// void winch_action(uint8_t ch3_clicks);
// bool abort_winching(void);

void process_channel_reversing_setup(void);
void reversing_setup_action(uint8_t ch3_clicks);

void output_preprocessor(void);

void init_gpio_lights(void);
void init_lights(void);
void process_lights(void);
void next_light_sequence(void);
void light_switch_up(void);
void light_switch_down(void);
void toggle_light_switch(void);

void process_shelf_queen_mode(void);
void set_shelf_queen_mode(bool state);

void init_light_programs(void);
void process_light_program_events(void);
uint32_t process_light_programs(void);
uint8_t get_priority_run_state(void);


uint16_t random_min_max(uint16_t min, uint16_t max);

#endif // __GLOBALS_H
